lucia-malickova/manta-chair/MANTA_LIGHT/27_SEG_13L.stl

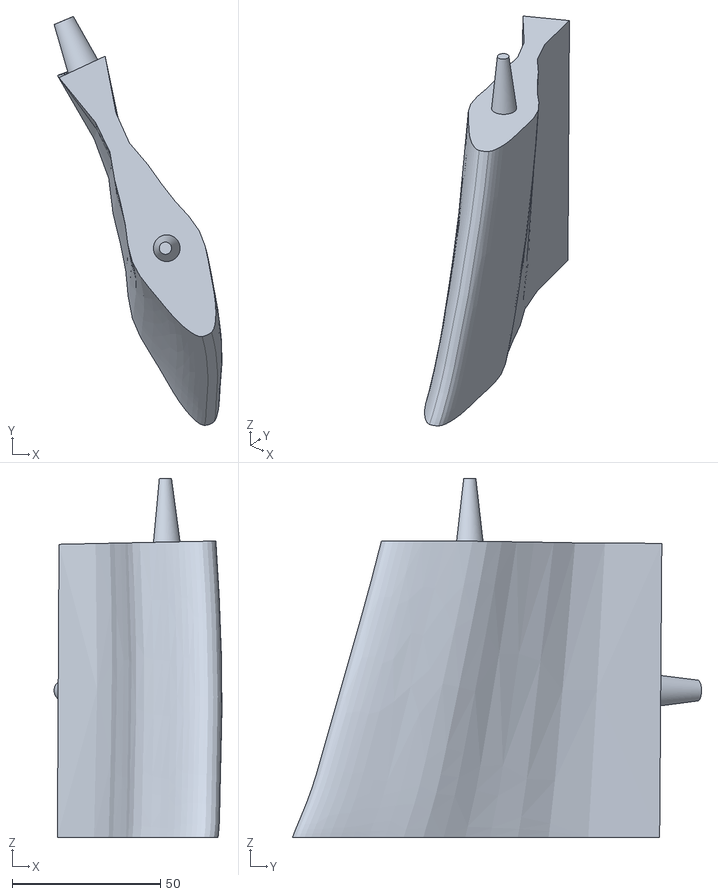
[picture p18: CAD file, 2026-09-29]
MANTA_LIGHT/27_SEG_13L.stl
56.6 x 138.1 x 121.2
