lucia-malickova/manta-chair/MANTA_RIBBON/41_SEG_22R.stl

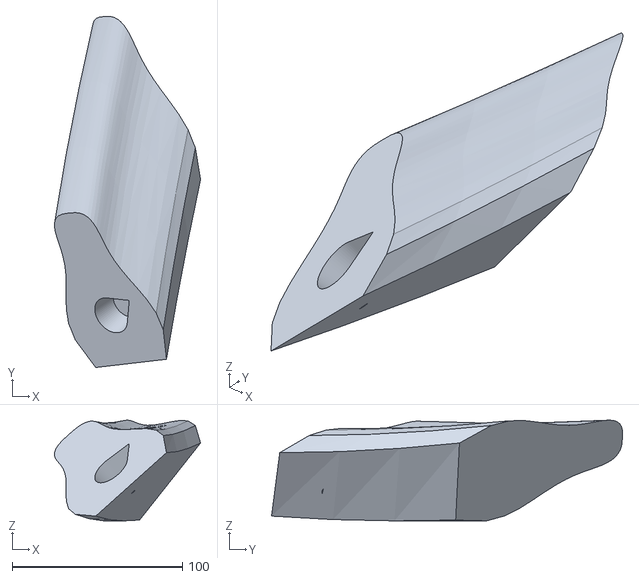
[picture p19: CAD file, 2026-09-29]
MANTA_RIBBON/41_SEG_22R.stl
85.9 x 206.4 x 59.2
