lucia-malickova/manta-chair/MANTA_LIGHT/04_SEG_01R.stl

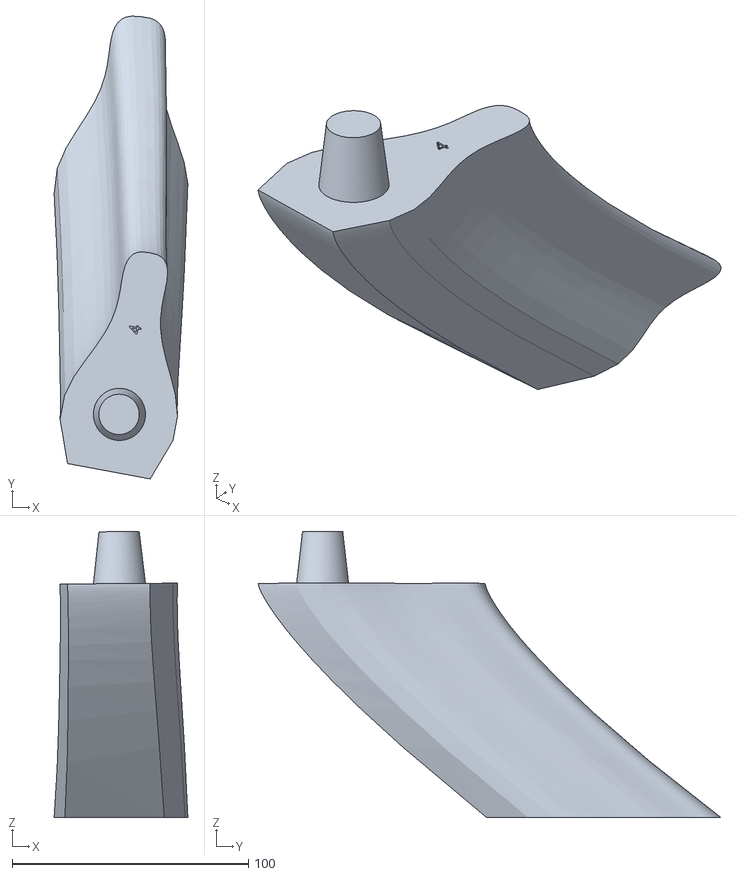
[picture p20: CAD file, 2026-09-29]
MANTA_LIGHT/04_SEG_01R.stl
56.7 x 196.1 x 121.2
