lucia-malickova/manta-chair/MANTA_RIBBON/26_SEG_12R.stl

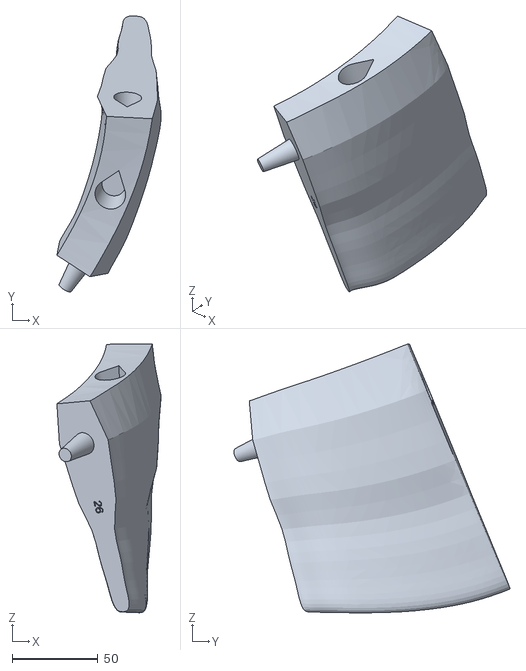
[picture p21: CAD file, 2026-09-29]
MANTA_RIBBON/26_SEG_12R.stl
60.6 x 160.6 x 156.3
