lucia-malickova/manta-chair/MANTA_LIGHT/03_SEG_01L.stl

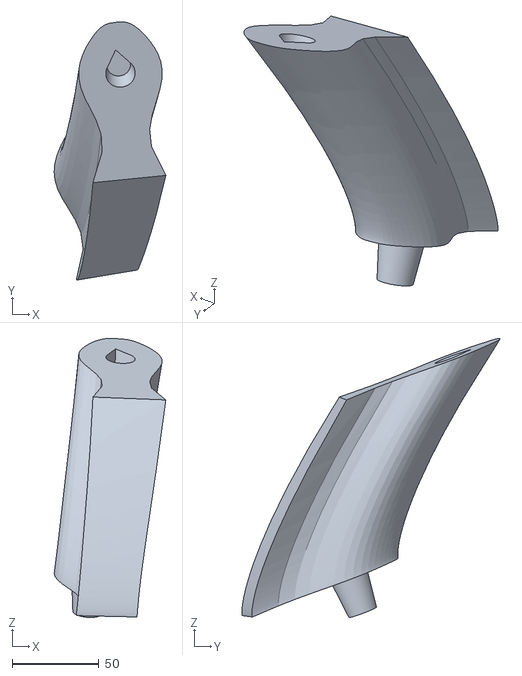
[picture p22: CAD file, 2026-09-29]
MANTA_LIGHT/03_SEG_01L.stl
64.5 x 149.1 x 161.1
