lucia-malickova/manta-chair/MANTA_RIBBON/29_SEG_14.stl

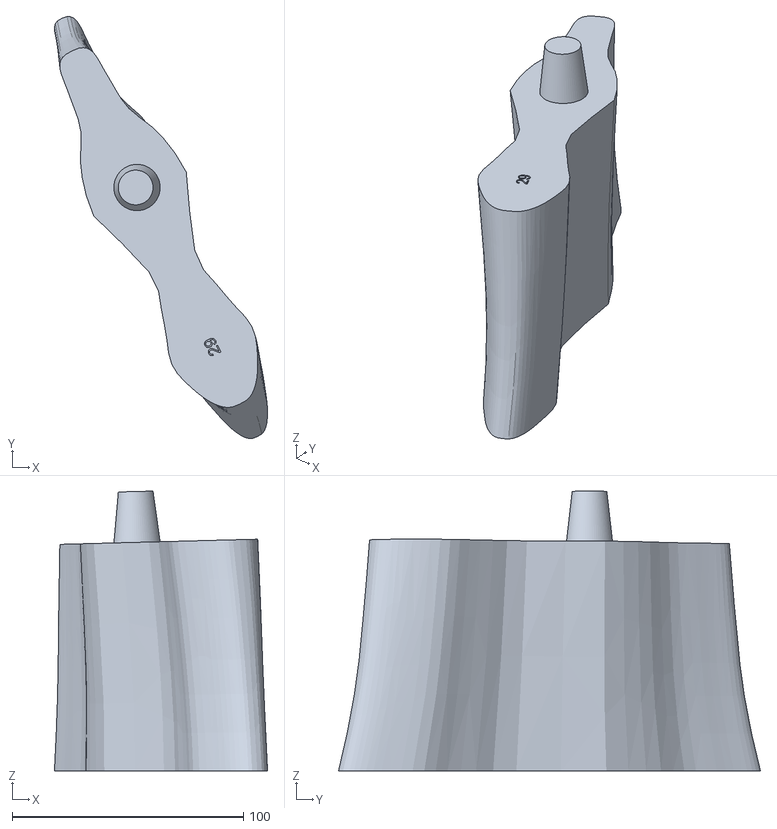
[picture p23: CAD file, 2026-09-29]
MANTA_RIBBON/29_SEG_14.stl
92.2 x 182.6 x 121.1
