lucia-malickova/manta-chair/MANTA_LIGHT/05_SEG_02L.stl

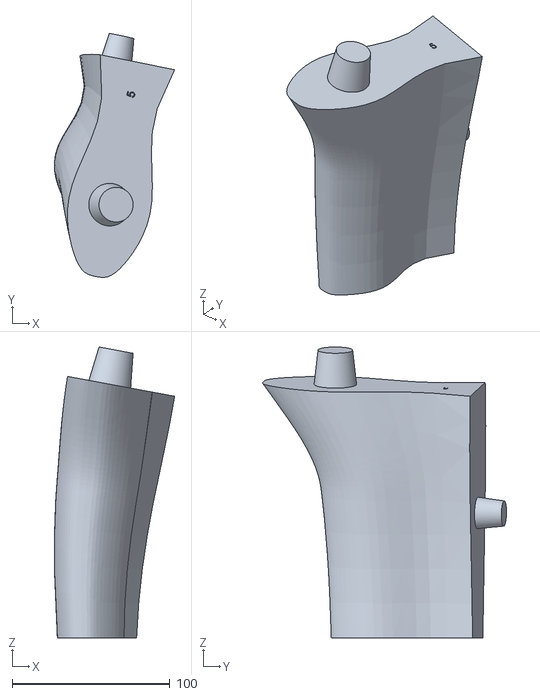
[picture p24: CAD file, 2026-09-29]
MANTA_LIGHT/05_SEG_02L.stl
76.4 x 154.9 x 184.7
