lucia-malickova/manta-chair/MANTA_RIBBON/07_SEG_03L.stl

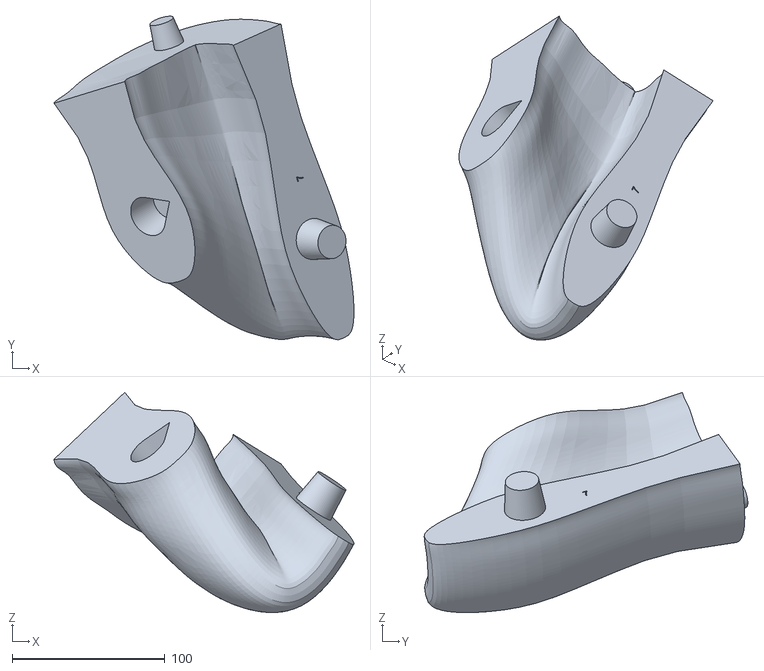
[picture p25: CAD file, 2026-09-29]
MANTA_RIBBON/07_SEG_03L.stl
196.5 x 212.0 x 144.2
