lucia-malickova/manta-chair/MANTA_LIGHT/17_SEG_08L.stl

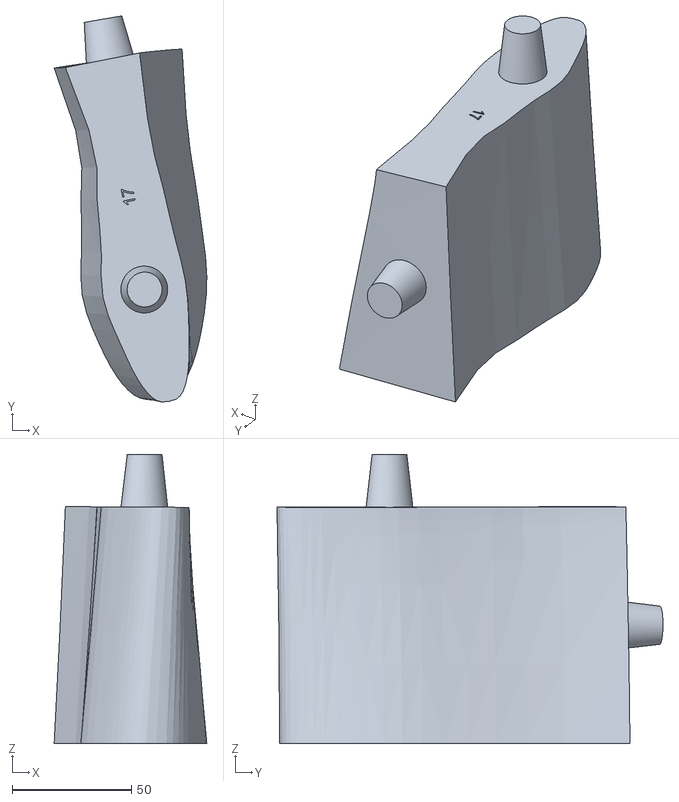
[picture p26: CAD file, 2026-09-29]
MANTA_LIGHT/17_SEG_08L.stl
63.9 x 161.6 x 121.0
