lucia-malickova/manta-chair/MANTA_RIBBON/09_SEG_04L.stl

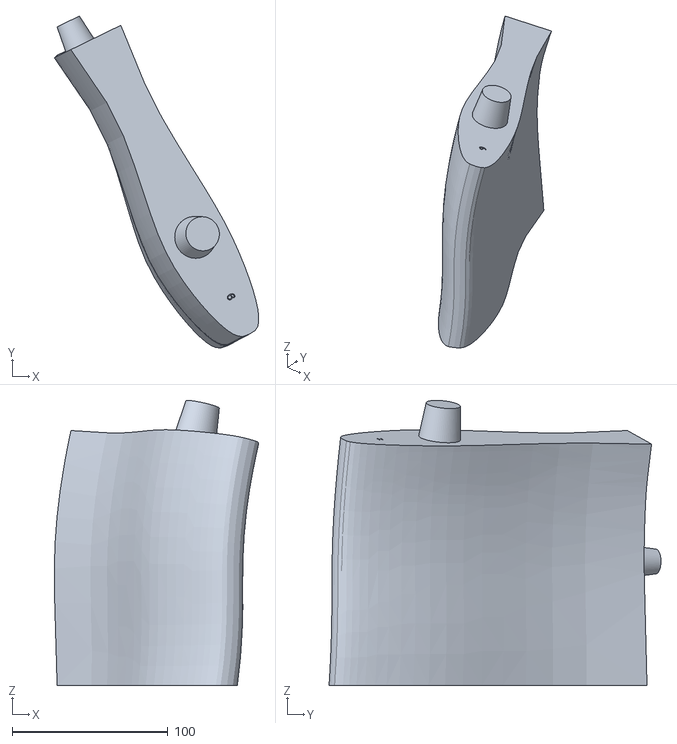
[picture p27: CAD file, 2026-09-29]
MANTA_RIBBON/09_SEG_04L.stl
131.2 x 213.1 x 183.1
