lucia-malickova/manta-chair/MANTA_LIGHT/40_SEG_22L.stl

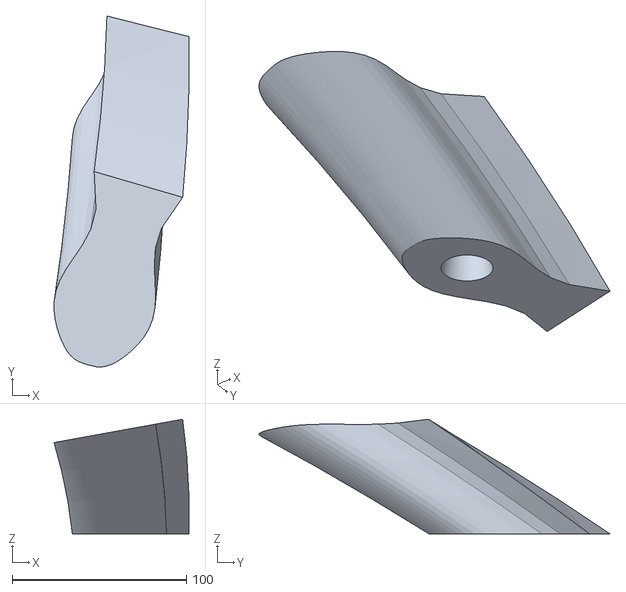
[picture p28: CAD file, 2026-09-29]
MANTA_LIGHT/40_SEG_22L.stl
77.3 x 201.2 x 65.7
