lucia-malickova/manta-chair/MANTA_RIBBON/19_SEG_09L.stl

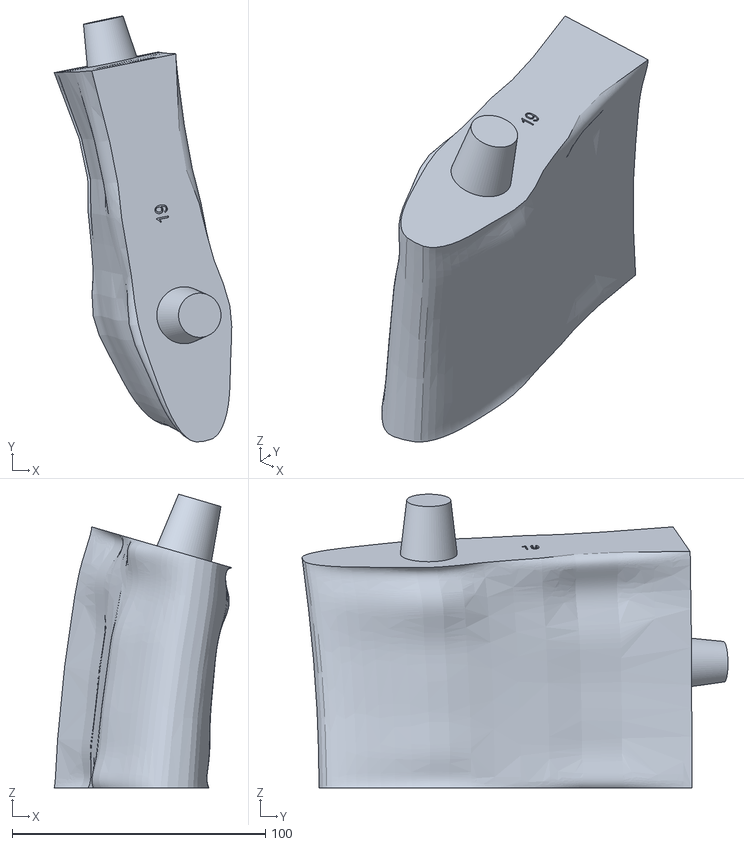
[picture p29: CAD file, 2026-09-29]
MANTA_RIBBON/19_SEG_09L.stl
70.2 x 168.3 x 116.0
