lucia-malickova/manta-chair/MANTA_LIGHT/02_SEG_00R.stl

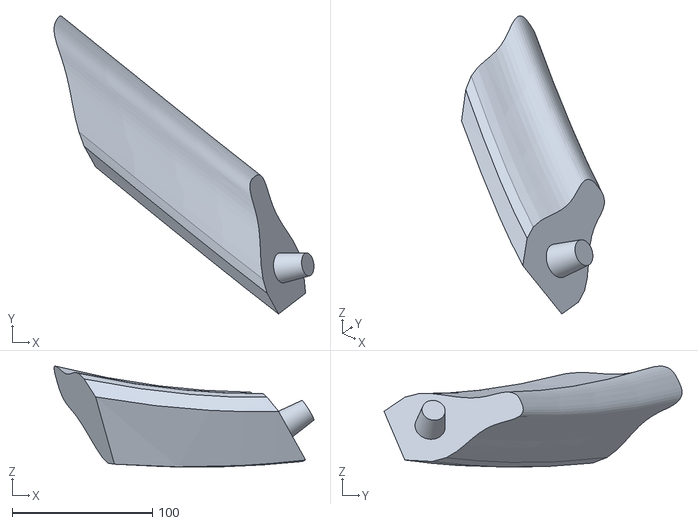
[picture p30: CAD file, 2026-09-29]
MANTA_LIGHT/02_SEG_00R.stl
185.1 x 212.2 x 71.7
