lucia-malickova/manta-chair/MANTA_RIBBON/04_SEG_01R.stl

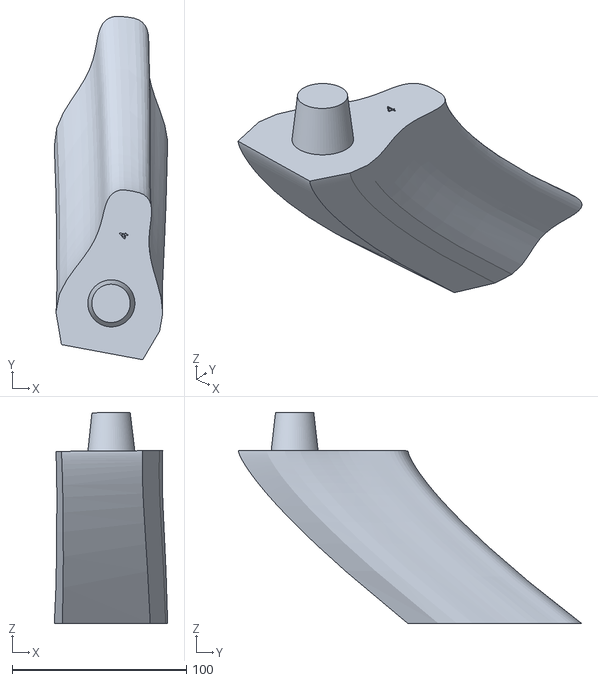
[picture p31: CAD file, 2026-09-29]
MANTA_RIBBON/04_SEG_01R.stl
65.1 x 197.3 x 121.2
