lucia-malickova/manta-chair/MANTA_LIGHT/06_SEG_02R.stl

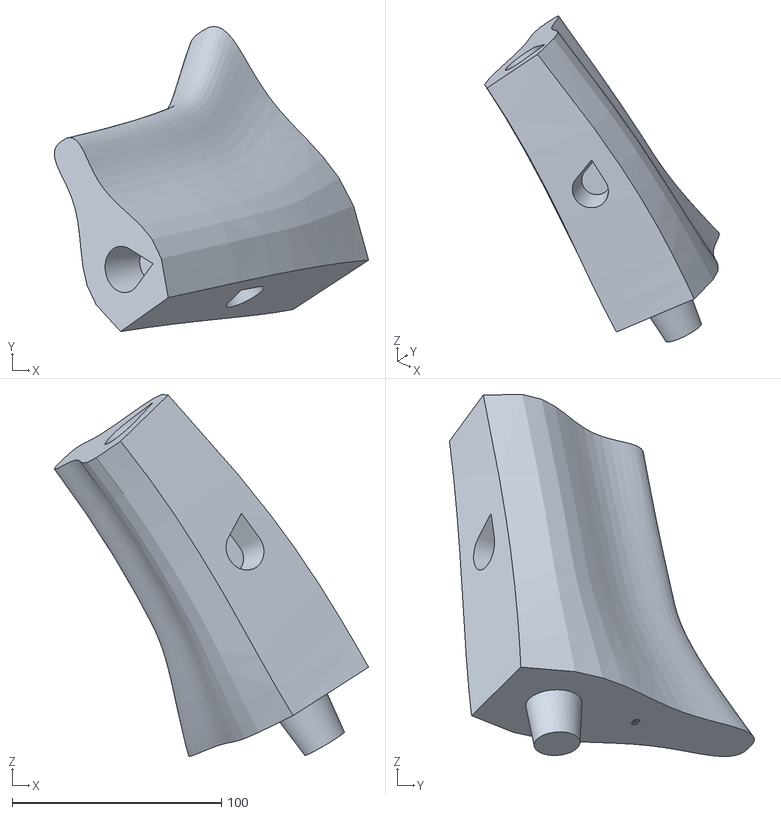
[picture p32: CAD file, 2026-09-29]
MANTA_LIGHT/06_SEG_02R.stl
150.3 x 145.9 x 173.1
