lucia-malickova/manta-chair/MANTA_RIBBON/20_SEG_09R.stl

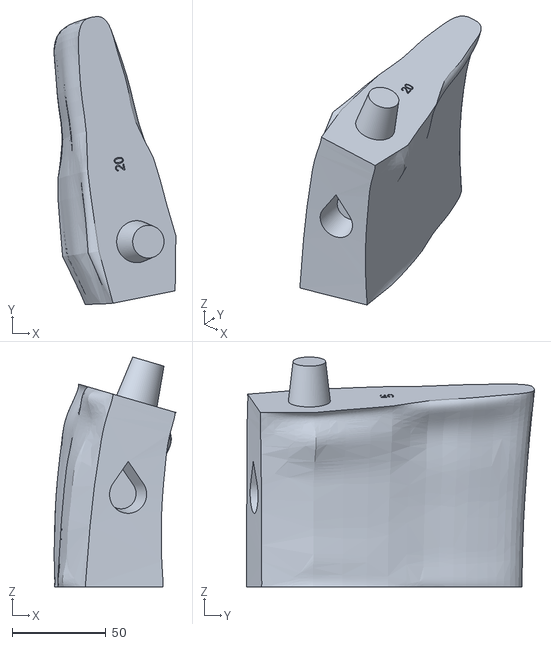
[picture p33: CAD file, 2026-09-29]
MANTA_RIBBON/20_SEG_09R.stl
65.1 x 154.0 x 122.9
