lucia-malickova/manta-chair/MANTA_LIGHT/10_SEG_04R.stl

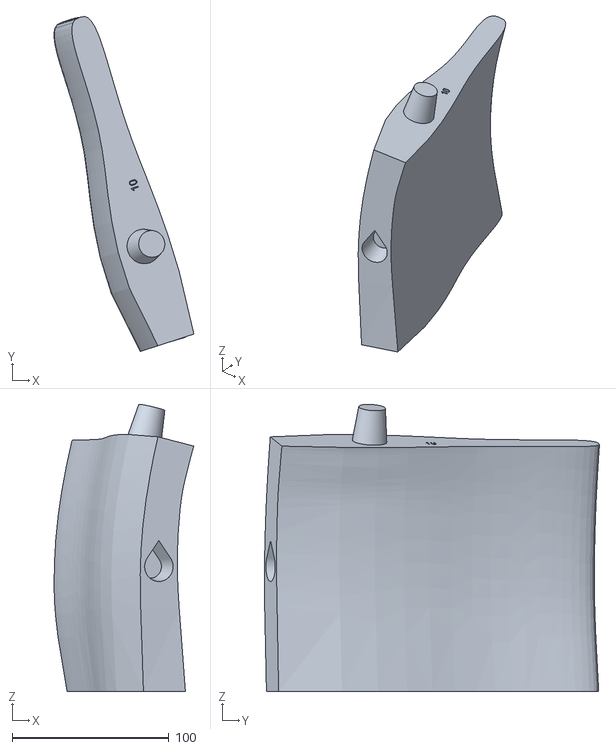
[picture p34: CAD file, 2026-09-29]
MANTA_LIGHT/10_SEG_04R.stl
89.1 x 213.4 x 183.0
