lucia-malickova/manta-chair/MANTA_RIBBON/32_SEG_17.stl

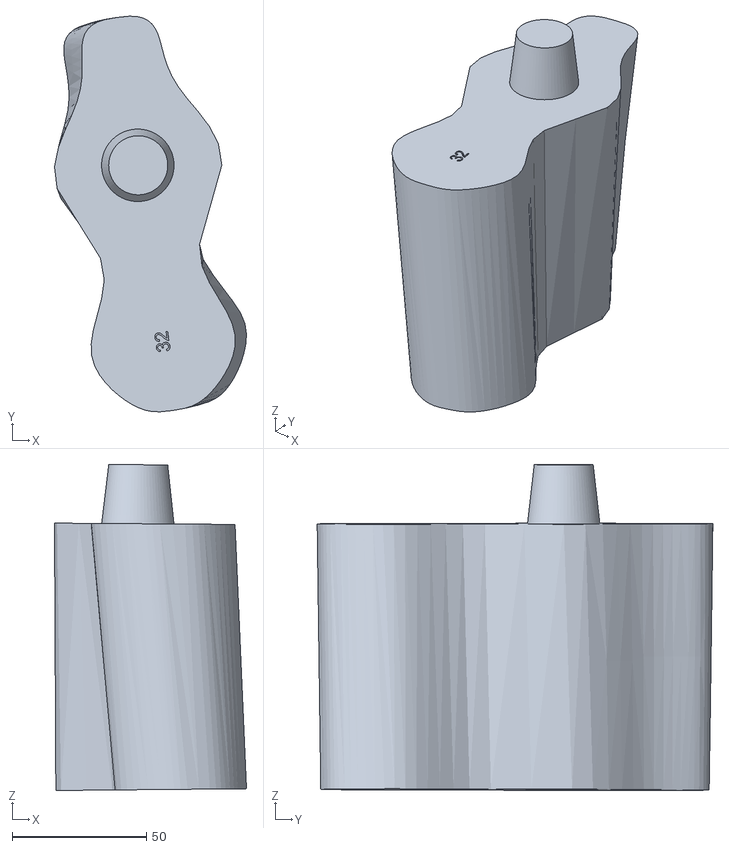
[picture p35: CAD file, 2026-09-29]
MANTA_RIBBON/32_SEG_17.stl
71.6 x 147.5 x 121.5
