lucia-malickova/manta-chair/MANTA_LIGHT/28_SEG_13R.stl

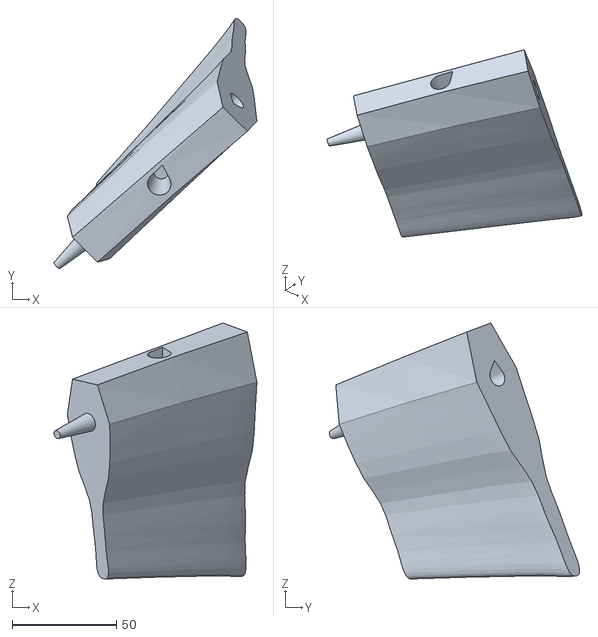
[picture p36: CAD file, 2026-09-29]
MANTA_LIGHT/28_SEG_13R.stl
97.5 x 120.3 x 123.0
