lucia-malickova/manta-chair/MANTA_RIBBON/35_SEG_19R.stl

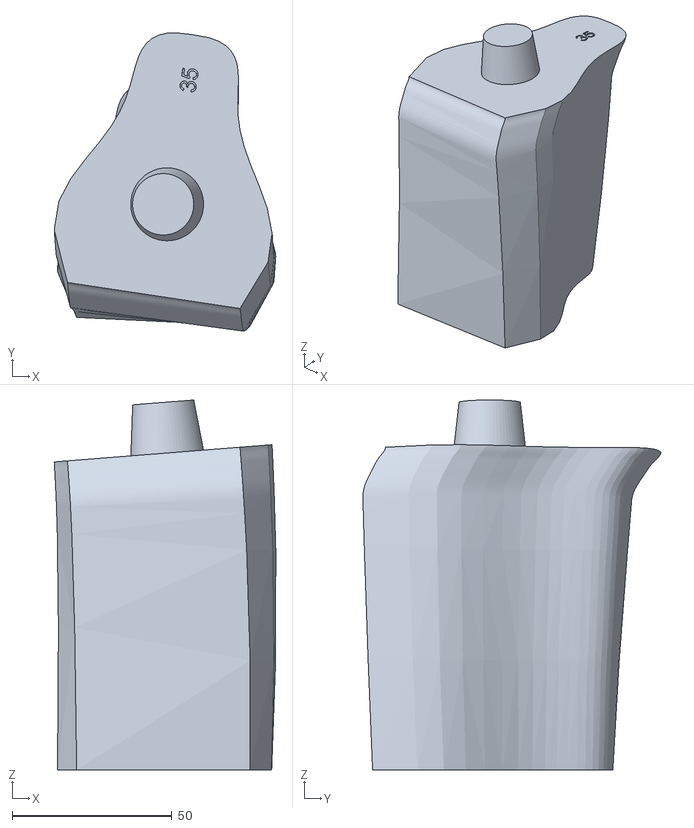
[picture p37: CAD file, 2026-09-29]
MANTA_RIBBON/35_SEG_19R.stl
69.5 x 93.5 x 116.0
