lucia-malickova/manta-chair/MANTA_LIGHT/33_SEG_18.stl

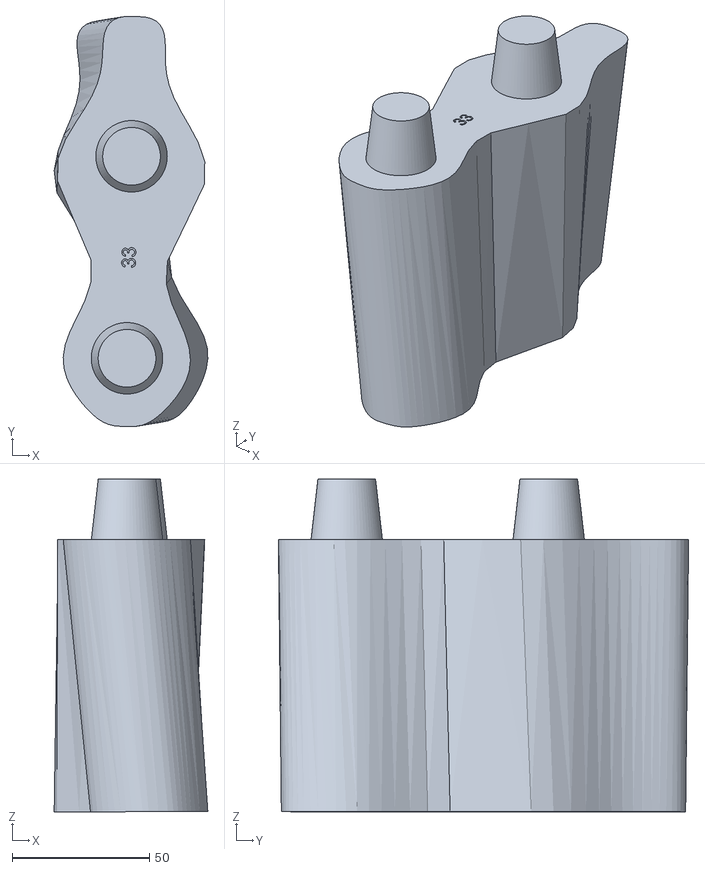
[picture p38: CAD file, 2026-09-29]
MANTA_LIGHT/33_SEG_18.stl
56.0 x 149.4 x 121.2
