lucia-malickova/manta-chair/MANTA_RIBBON/06_SEG_02R.stl

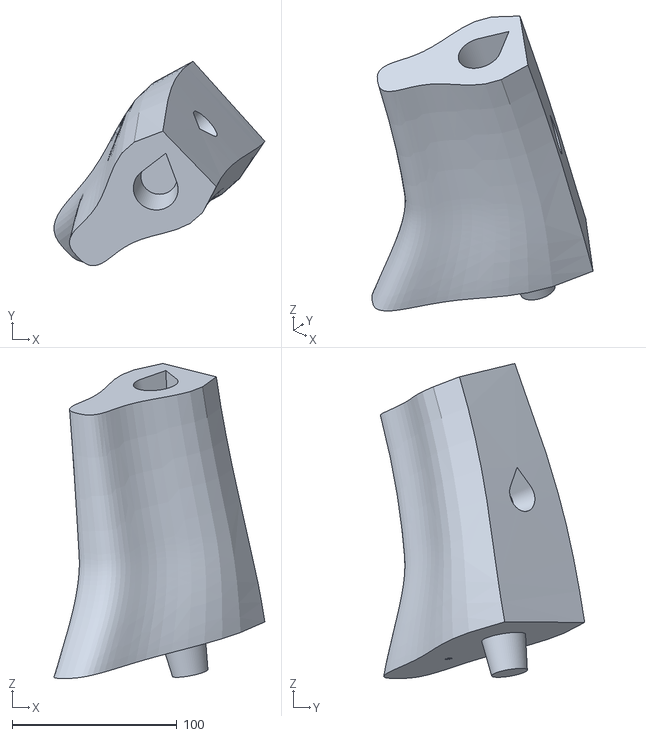
[picture p39: CAD file, 2026-09-29]
MANTA_RIBBON/06_SEG_02R.stl
128.1 x 124.2 x 191.4
