lucia-malickova/manta-chair/MANTA_LIGHT/34_SEG_19L.stl

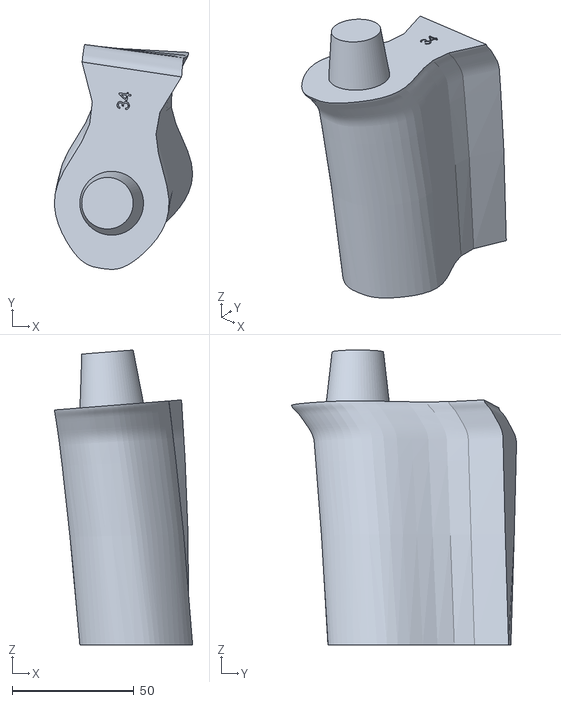
[picture p40: CAD file, 2026-09-29]
MANTA_LIGHT/34_SEG_19L.stl
56.8 x 92.4 x 121.2
