lucia-malickova/manta-chair/MANTA_RIBBON/33_SEG_18.stl

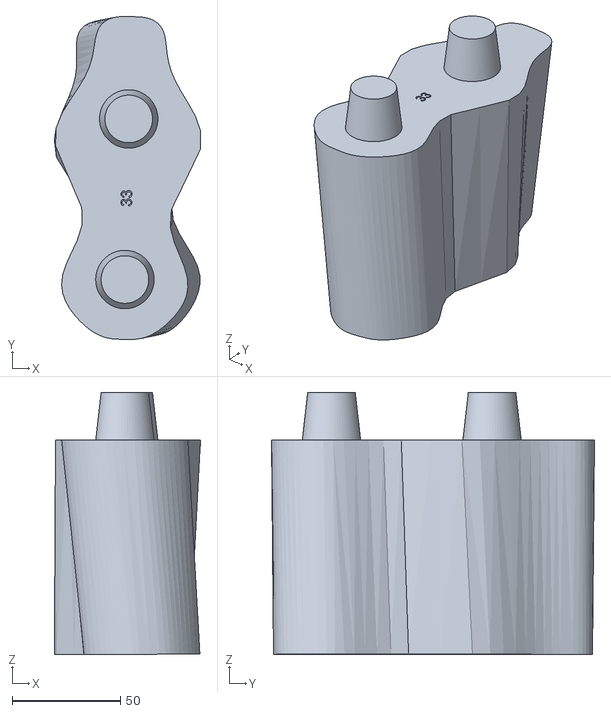
[picture p41: CAD file, 2026-09-29]
MANTA_RIBBON/33_SEG_18.stl
67.7 x 149.4 x 121.3
