lucia-malickova/manta-chair/MANTA_LIGHT/22_SEG_10R.stl

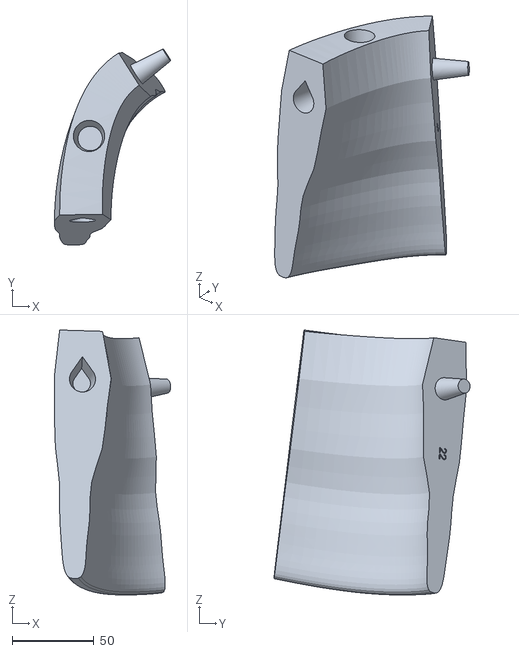
[picture p42: CAD file, 2026-09-29]
MANTA_LIGHT/22_SEG_10R.stl
71.0 x 119.6 x 161.6
