lucia-malickova/manta-chair/MANTA_RIBBON/37_SEG_20R.stl

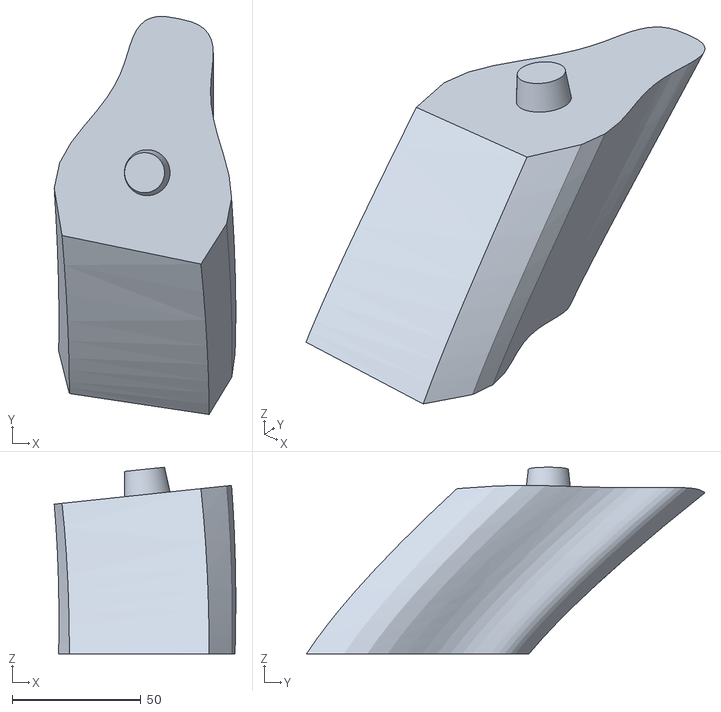
[picture p43: CAD file, 2026-09-29]
MANTA_RIBBON/37_SEG_20R.stl
70.5 x 154.5 x 72.4
