lucia-malickova/manta-chair/MANTA_LIGHT/37_SEG_20R.stl

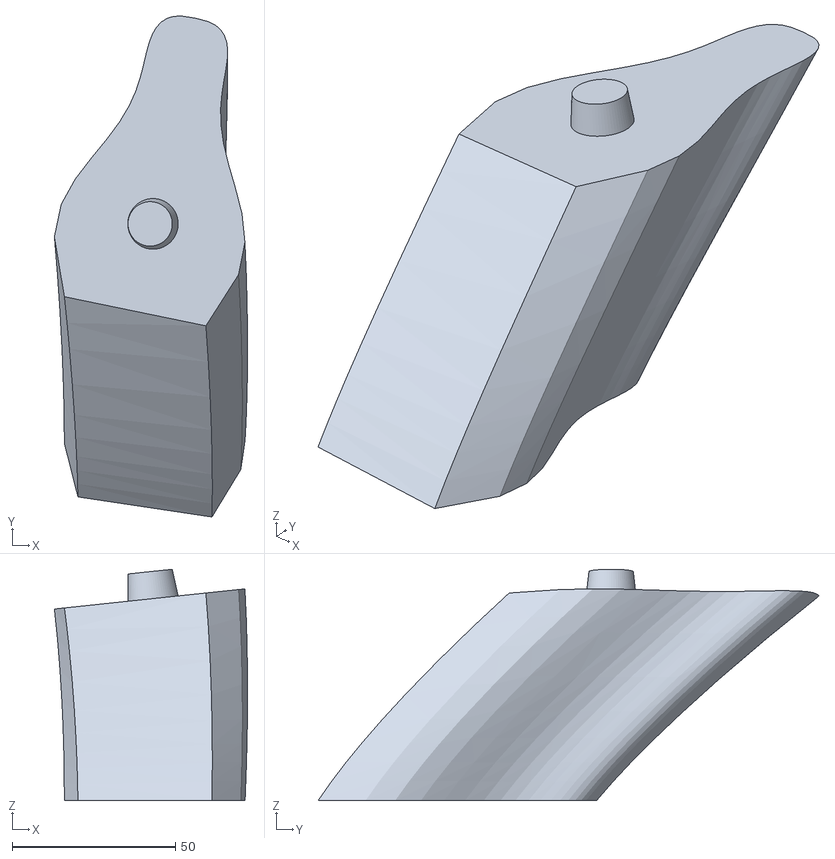
[picture p44: CAD file, 2026-09-29]
MANTA_LIGHT/37_SEG_20R.stl
59.1 x 153.3 x 70.8
