lucia-malickova/manta-chair/MANTA_RIBBON/11_SEG_05L.stl

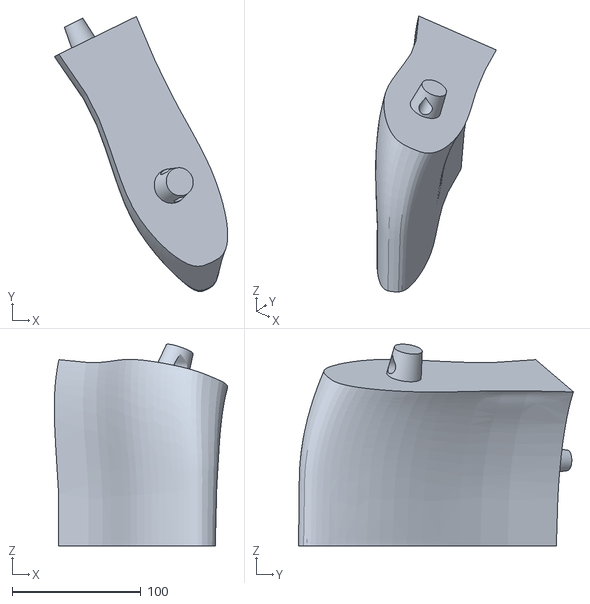
[picture p45: CAD file, 2026-09-29]
MANTA_RIBBON/11_SEG_05L.stl
134.5 x 213.2 x 156.4
