lucia-malickova/manta-chair/MANTA_LIGHT/08_SEG_03R.stl

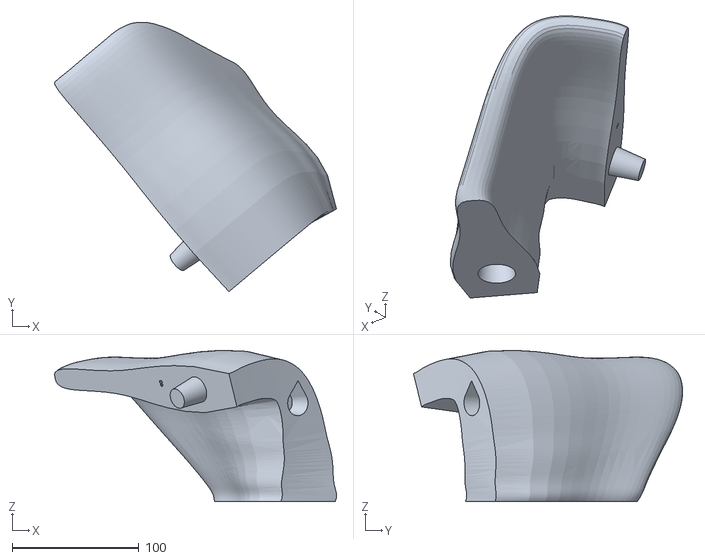
[picture p46: CAD file, 2026-09-29]
MANTA_LIGHT/08_SEG_03R.stl
222.8 x 212.7 x 119.6
