lucia-malickova/manta-chair/MANTA_RIBBON/30_SEG_15.stl

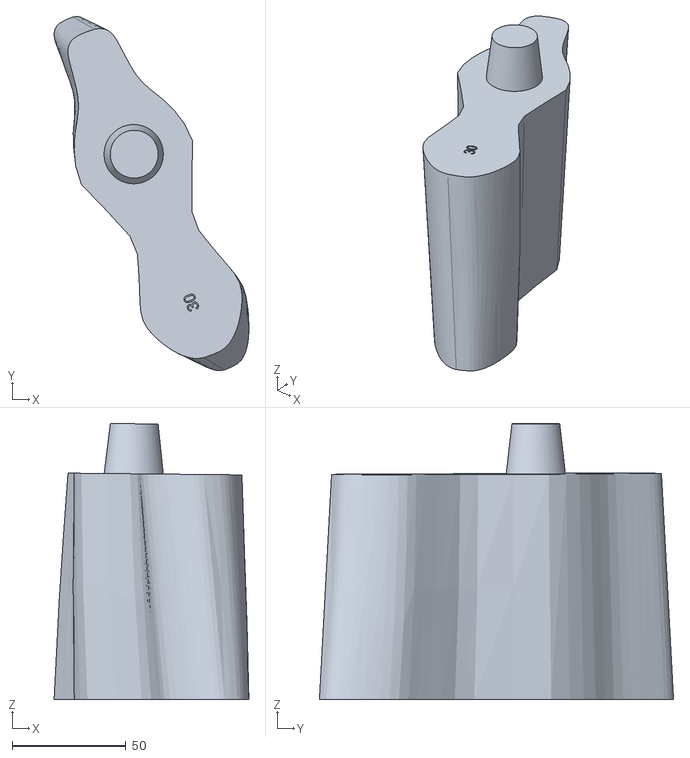
[picture p47: CAD file, 2026-09-29]
MANTA_RIBBON/30_SEG_15.stl
85.7 x 155.7 x 121.3
