lucia-malickova/manta-chair/MANTA_LIGHT/11_SEG_05L.stl

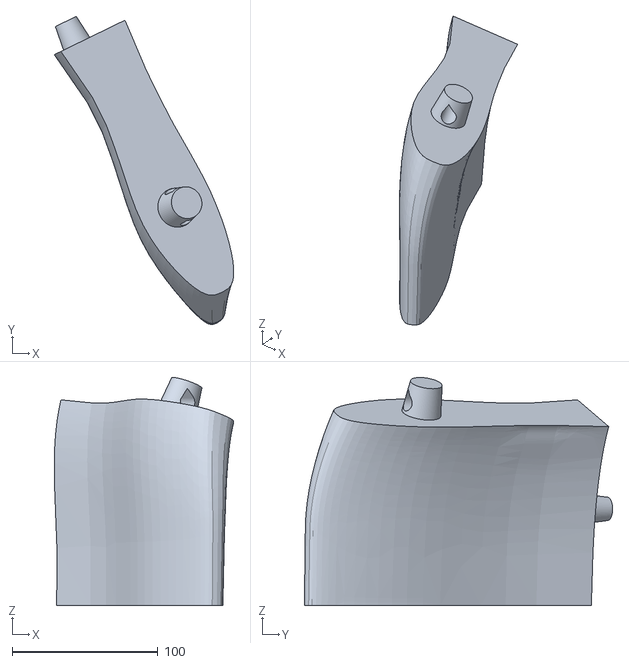
[picture p48: CAD file, 2026-09-29]
MANTA_LIGHT/11_SEG_05L.stl
123.1 x 211.4 x 156.4
