lucia-malickova/manta-chair/MANTA_RIBBON/27_SEG_13L.stl

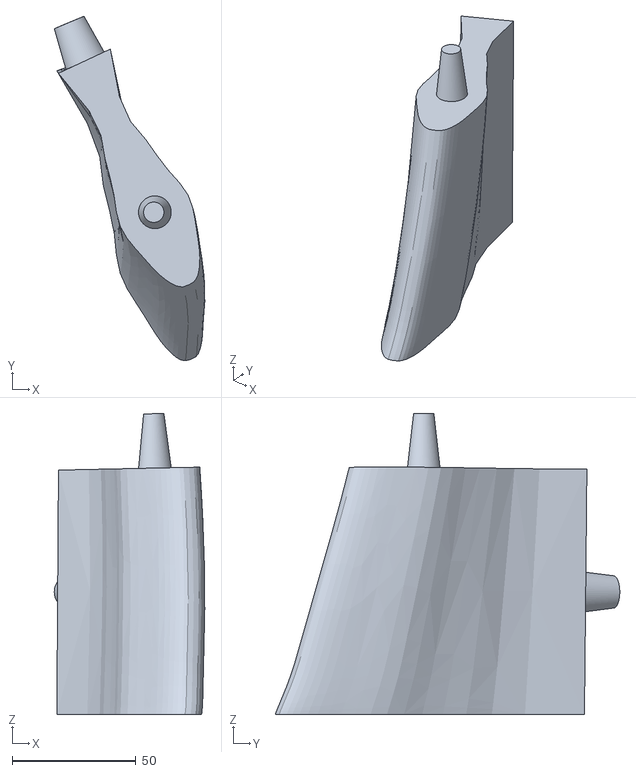
[picture p49: CAD file, 2026-09-29]
MANTA_RIBBON/27_SEG_13L.stl
60.9 x 139.5 x 121.8
