lucia-malickova/manta-chair/MANTA_LIGHT/21_SEG_10L.stl

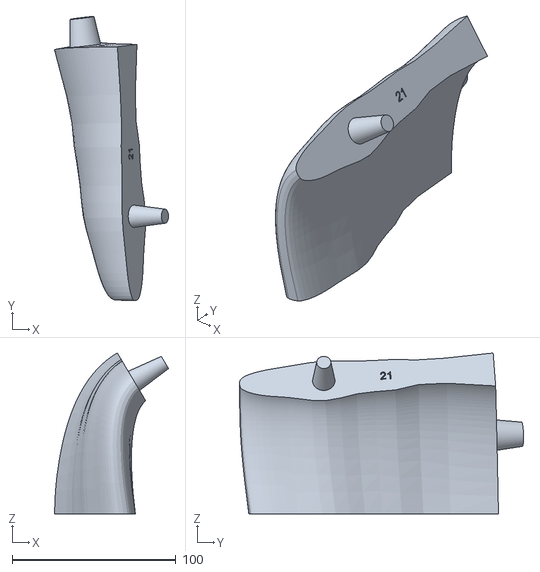
[picture p50: CAD file, 2026-09-29]
MANTA_LIGHT/21_SEG_10L.stl
69.6 x 173.3 x 98.2
