lucia-malickova/manta-chair/MANTA_RIBBON/22_SEG_10R.stl

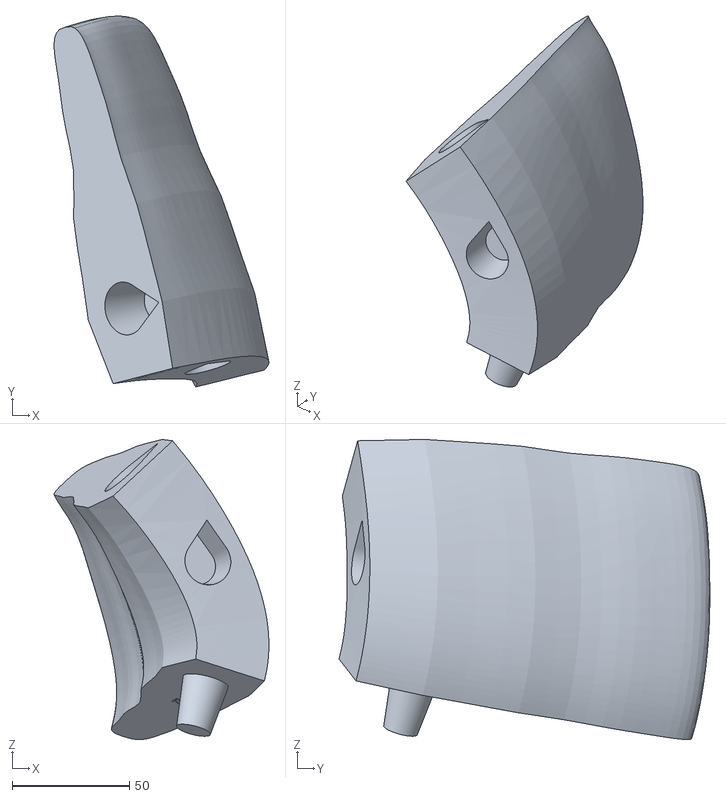
[picture p51: CAD file, 2026-09-29]
MANTA_RIBBON/22_SEG_10R.stl
91.6 x 158.2 x 127.9
