lucia-malickova/manta-chair/MANTA_LIGHT/24_SEG_11R.stl

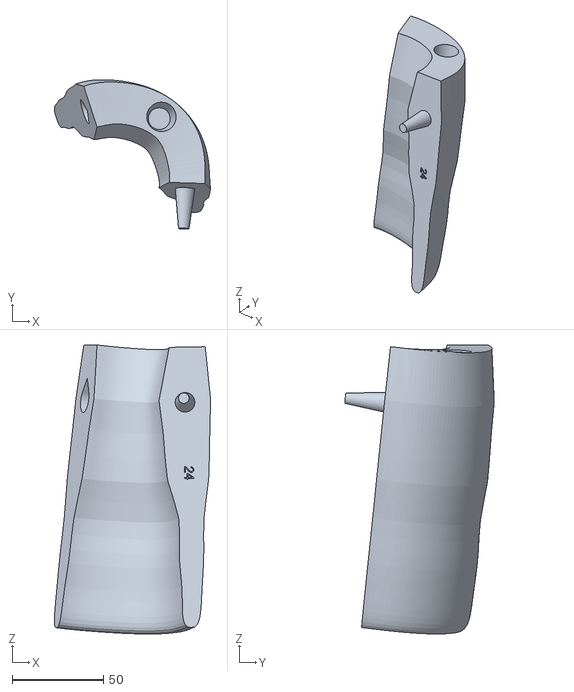
[picture p52: CAD file, 2026-09-29]
MANTA_LIGHT/24_SEG_11R.stl
85.4 x 81.7 x 158.0
