lucia-malickova/manta-chair/MANTA_RIBBON/14_SEG_06R.stl

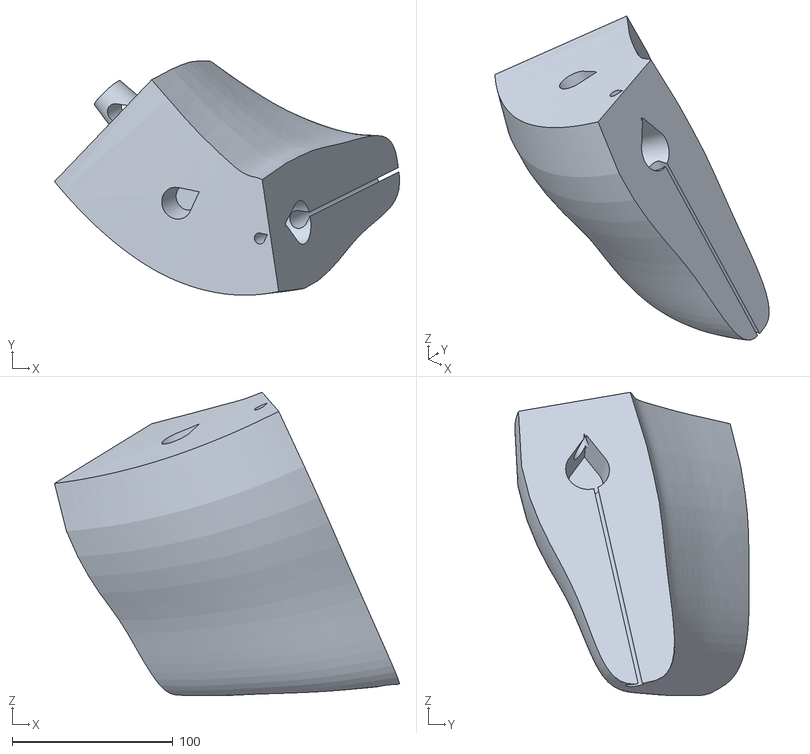
[picture p53: CAD file, 2026-09-29]
MANTA_RIBBON/14_SEG_06R.stl
214.6 x 145.8 x 188.7
