lucia-malickova/manta-chair/MANTA_LIGHT/15_SEG_07L.stl

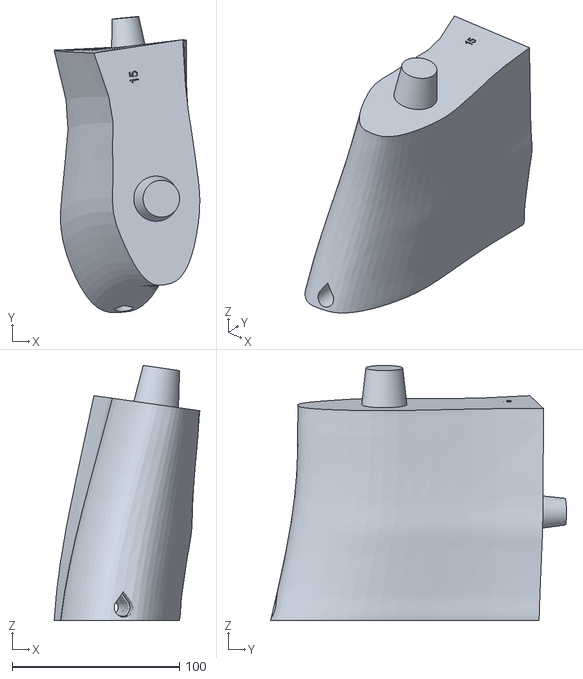
[picture p54: CAD file, 2026-09-29]
MANTA_LIGHT/15_SEG_07L.stl
87.1 x 176.8 x 152.4
