lucia-malickova/manta-chair/MANTA_RIBBON/38_SEG_21L.stl

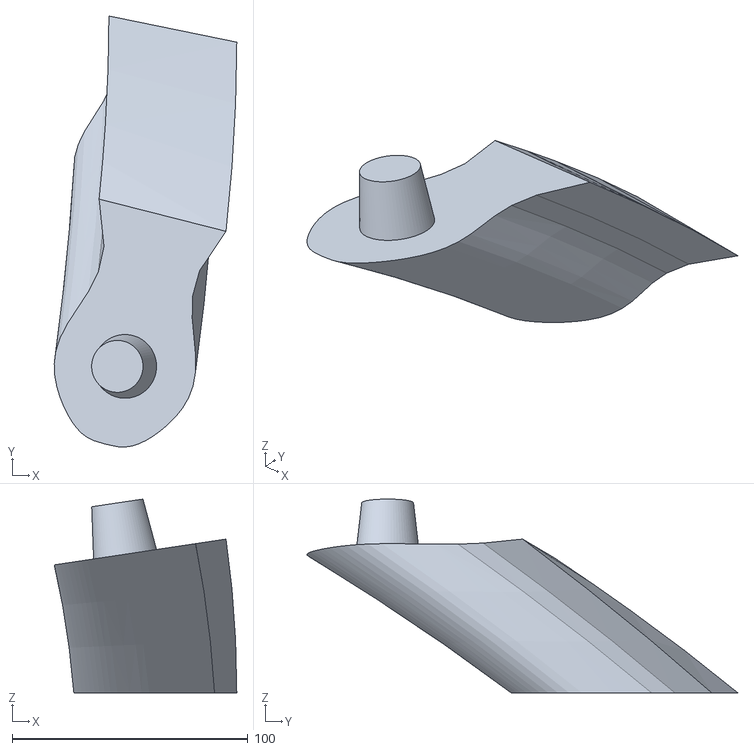
[picture p55: CAD file, 2026-09-29]
MANTA_RIBBON/38_SEG_21L.stl
77.4 x 182.7 x 82.2
