lucia-malickova/manta-chair/MANTA_LIGHT/41_SEG_22R.stl

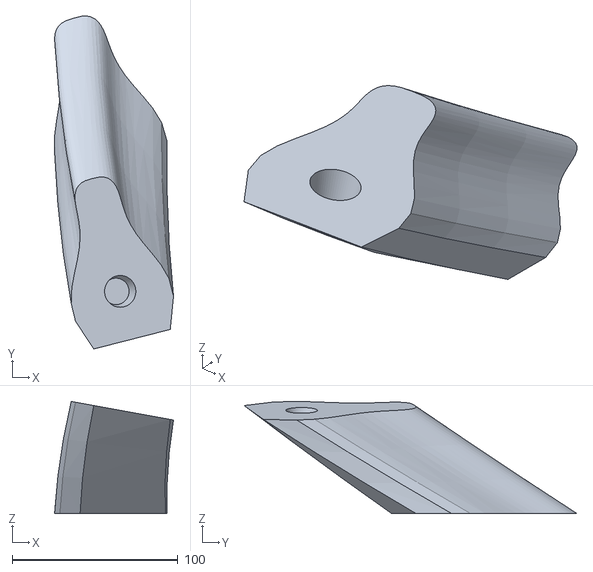
[picture p56: CAD file, 2026-09-29]
MANTA_LIGHT/41_SEG_22R.stl
71.9 x 201.1 x 67.7
