lucia-malickova/manta-chair/MANTA_RIBBON/36_SEG_20L.stl

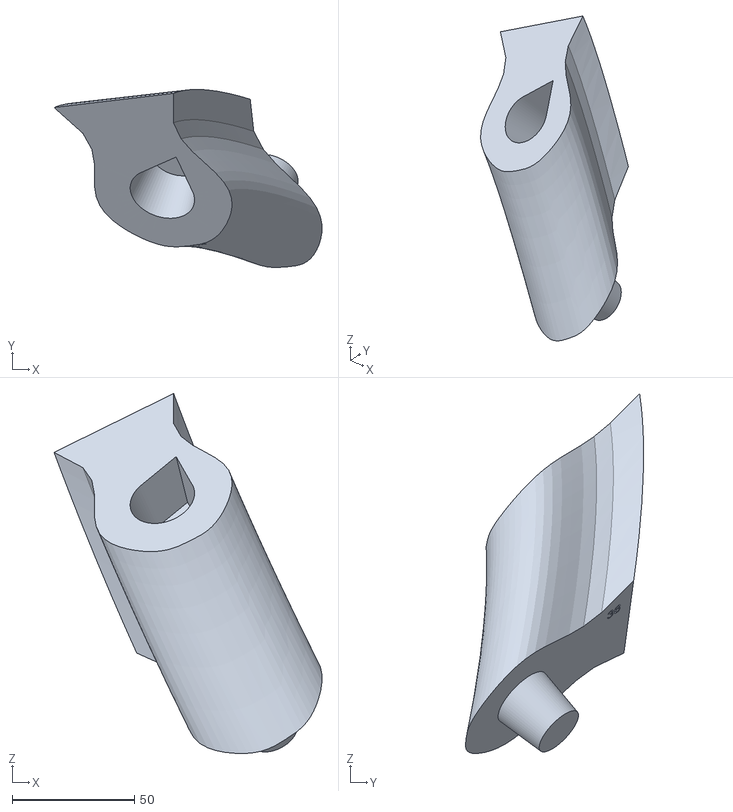
[picture p57: CAD file, 2026-09-29]
MANTA_RIBBON/36_SEG_20L.stl
109.6 x 72.9 x 147.3
