lucia-malickova/manta-chair/MANTA_LIGHT/19_SEG_09L.stl

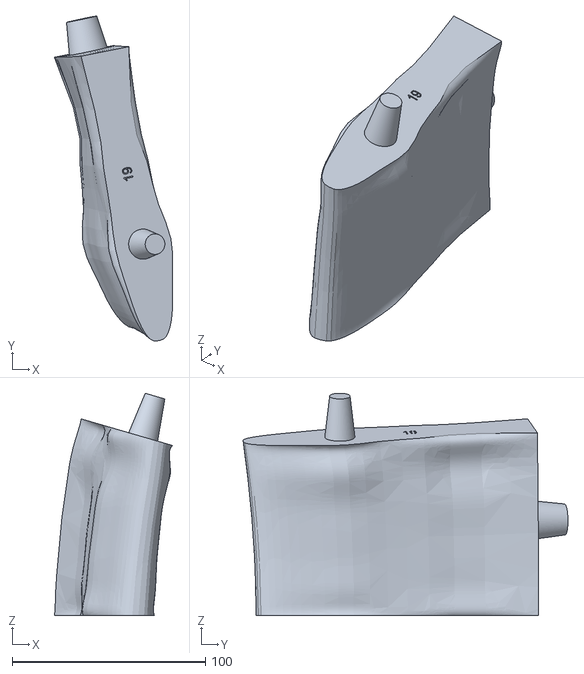
[picture p58: CAD file, 2026-09-29]
MANTA_LIGHT/19_SEG_09L.stl
61.2 x 168.1 x 115.1
