lucia-malickova/manta-chair/MANTA_RIBBON/16_SEG_07R.stl

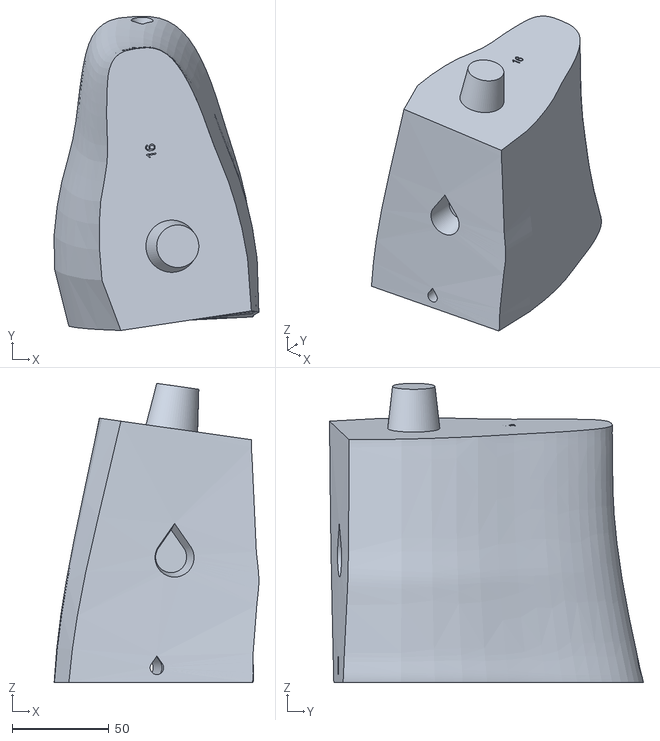
[picture p59: CAD file, 2026-09-29]
MANTA_RIBBON/16_SEG_07R.stl
106.0 x 162.5 x 155.0
