lucia-malickova/manta-chair/MANTA_LIGHT/20_SEG_09R.stl

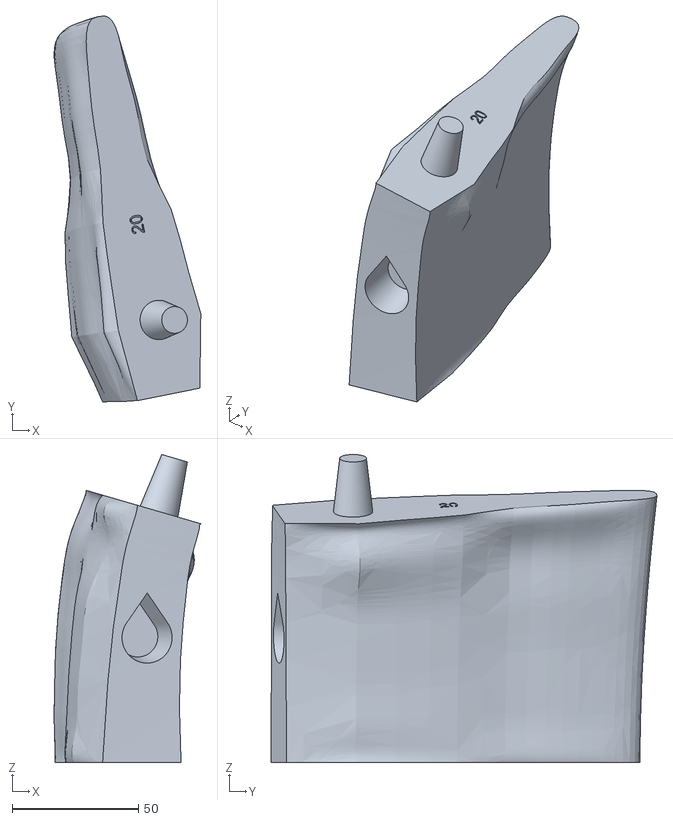
[picture p60: CAD file, 2026-09-29]
MANTA_LIGHT/20_SEG_09R.stl
58.1 x 152.8 x 122.0
