lucia-malickova/manta-chair/MANTA_RIBBON/10_SEG_04R.stl

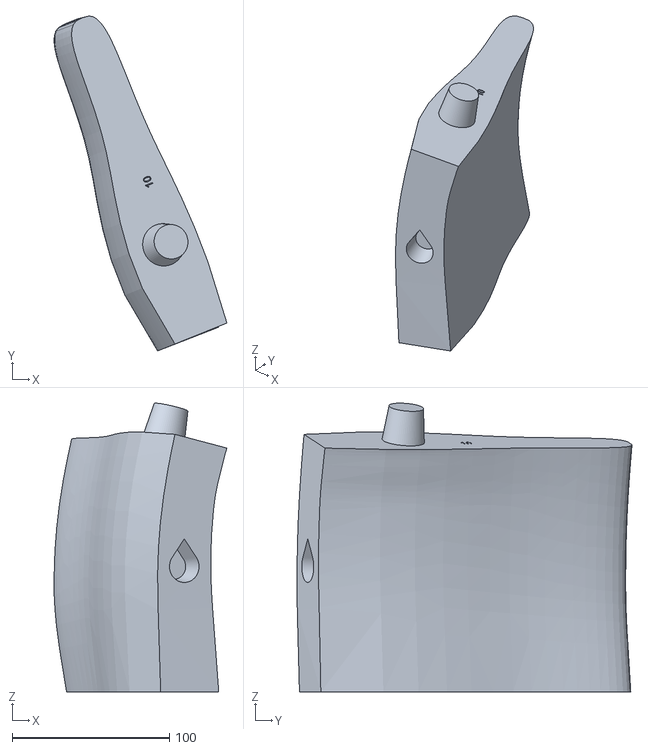
[picture p61: CAD file, 2026-09-29]
MANTA_RIBBON/10_SEG_04R.stl
109.9 x 213.0 x 183.6
