lucia-malickova/manta-chair/MANTA_LIGHT/26_SEG_12R.stl

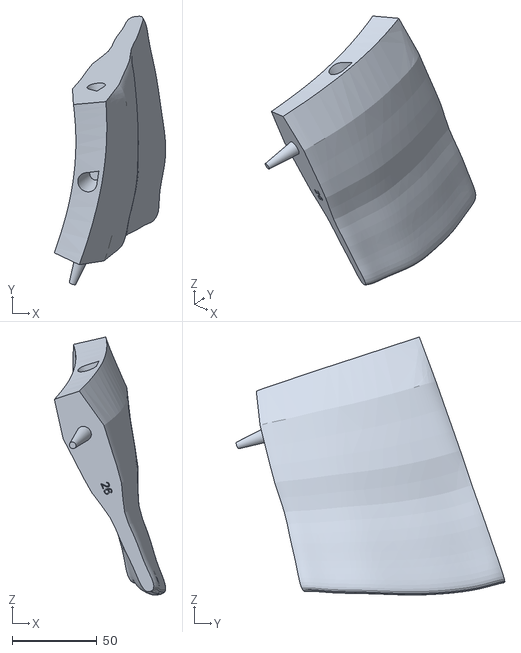
[picture p62: CAD file, 2026-09-29]
MANTA_LIGHT/26_SEG_12R.stl
65.7 x 158.6 x 152.3
