lucia-malickova/manta-chair/MANTA_RIBBON/42_PIN.stl

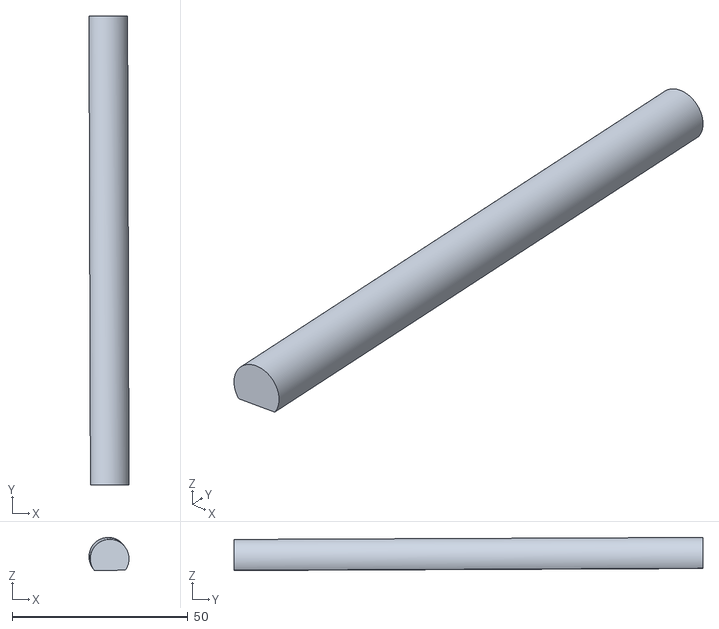
[picture p63: CAD file, 2026-09-29]
MANTA_RIBBON/42_PIN.stl
11.4 x 133.5 x 9.43
