lucia-malickova/manta-chair/MANTA_LIGHT/23_SEG_11L.stl

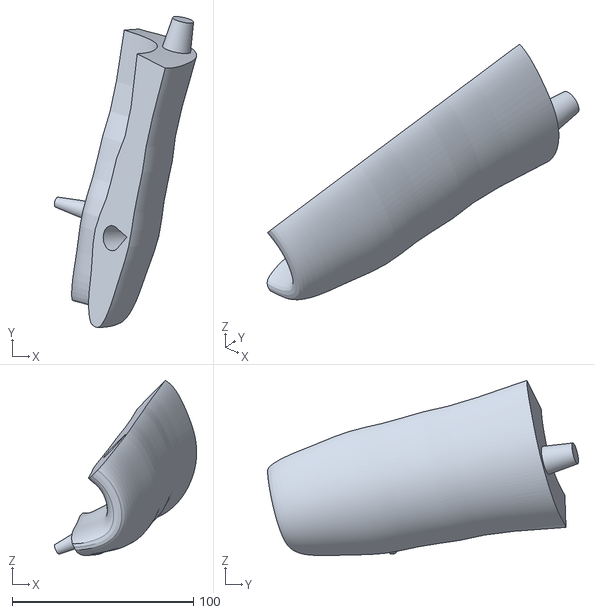
[picture p64: CAD file, 2026-09-29]
MANTA_LIGHT/23_SEG_11L.stl
78.4 x 171.4 x 96.6
