lucia-malickova/manta-chair/MANTA_RIBBON/21_SEG_10L.stl

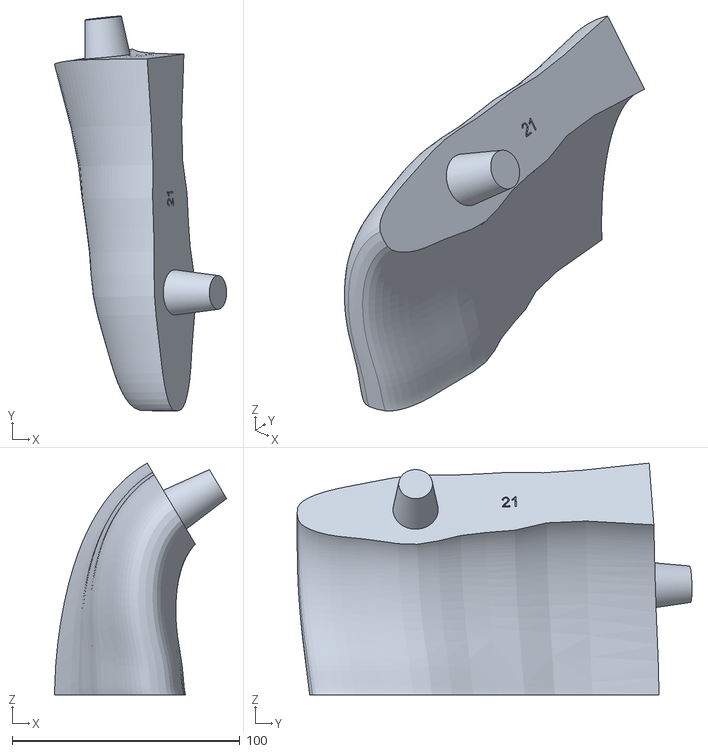
[picture p65: CAD file, 2026-09-29]
MANTA_RIBBON/21_SEG_10L.stl
75.6 x 173.3 x 101.7
