lucia-malickova/manta-chair/MANTA_LIGHT/16_SEG_07R.stl

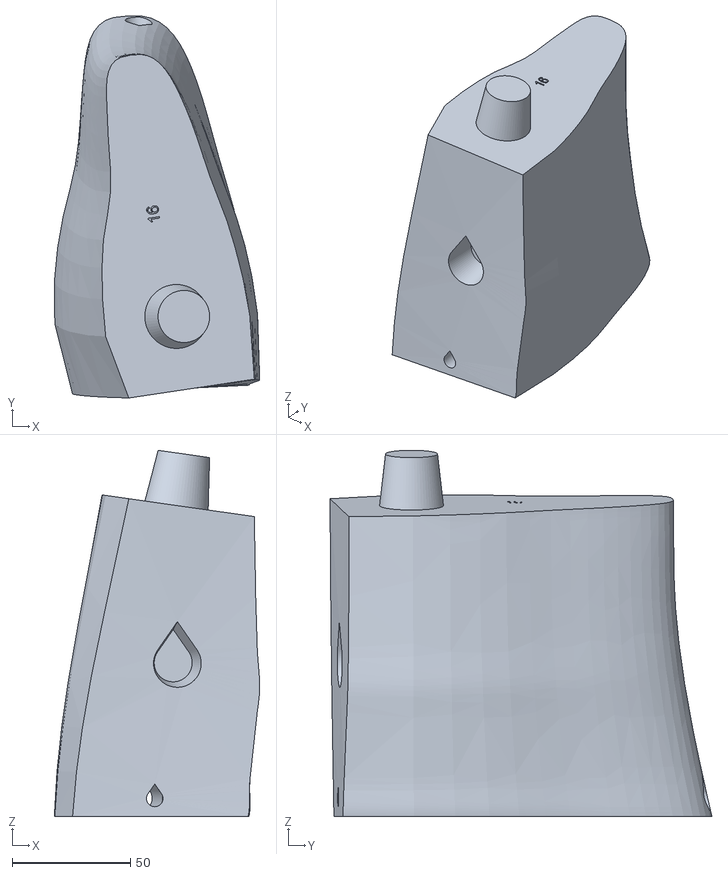
[picture p66: CAD file, 2026-09-29]
MANTA_LIGHT/16_SEG_07R.stl
86.8 x 161.4 x 154.8
