lucia-malickova/manta-chair/MANTA_RIBBON/17_SEG_08L.stl

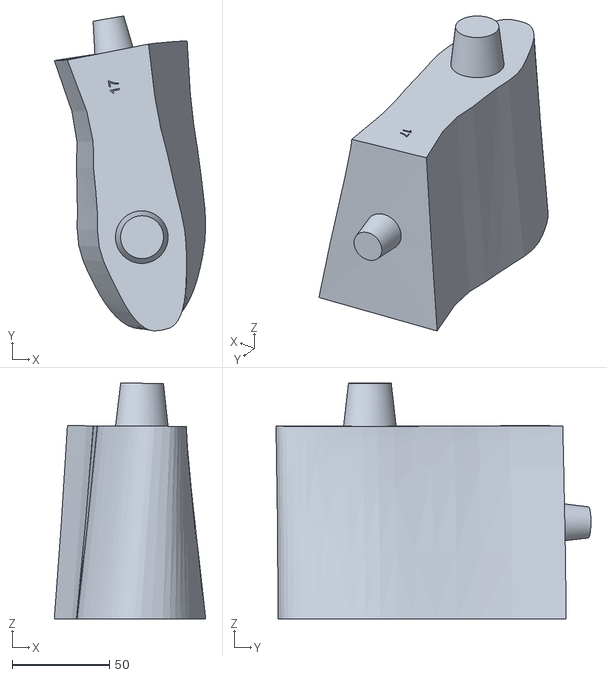
[picture p67: CAD file, 2026-09-29]
MANTA_RIBBON/17_SEG_08L.stl
77.8 x 161.7 x 121.1
