lucia-malickova/manta-chair/MANTA_LIGHT/01_SEG_00L.stl

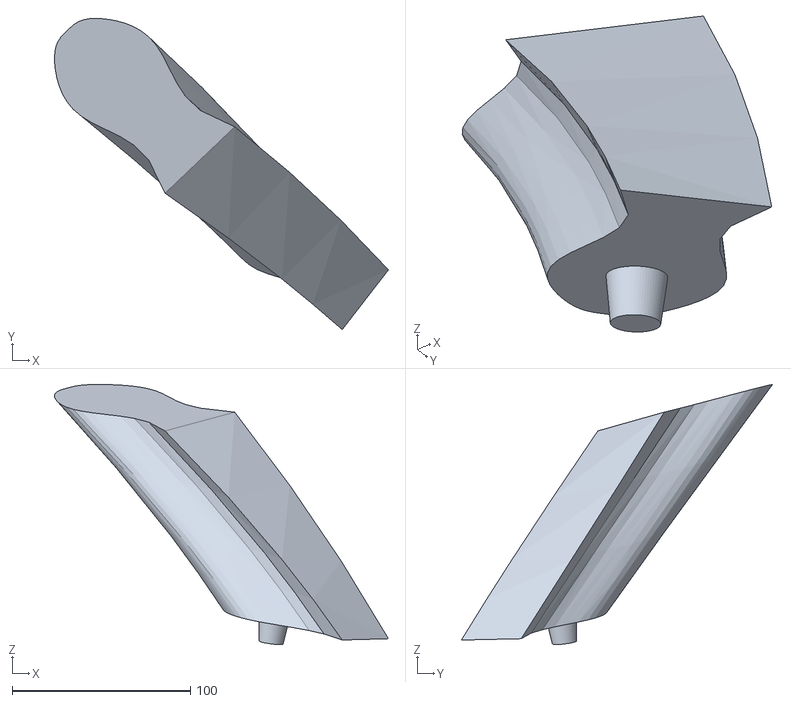
[picture p68: CAD file, 2026-09-29]
MANTA_LIGHT/01_SEG_00L.stl
187.2 x 174.4 x 145.8
