lucia-malickova/manta-chair/MANTA_RIBBON/02_SEG_00R.stl

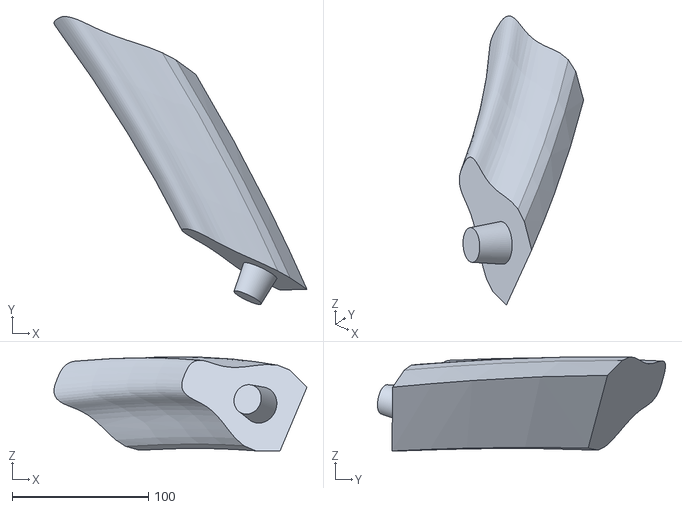
[picture p69: CAD file, 2026-09-29]
MANTA_RIBBON/02_SEG_00R.stl
185.8 x 211.5 x 69.0
