lucia-malickova/manta-chair/MANTA_LIGHT/14_SEG_06R.stl

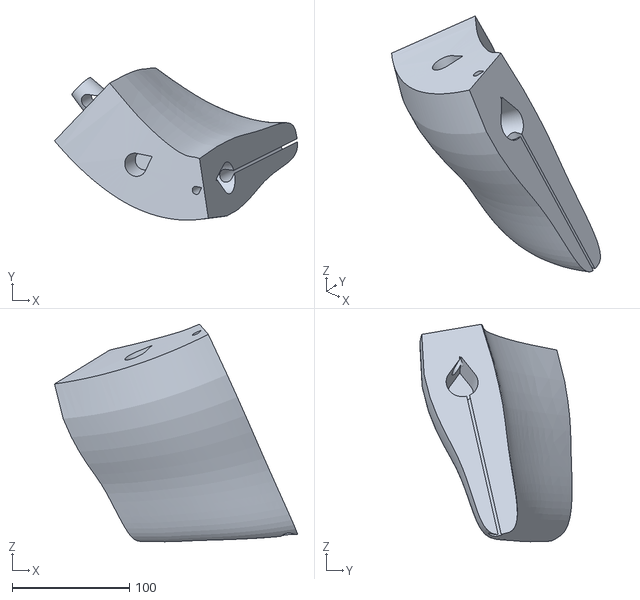
[picture p70: CAD file, 2026-09-29]
MANTA_LIGHT/14_SEG_06R.stl
207.6 x 130.0 x 185.9
