lucia-malickova/manta-chair/MANTA_RIBBON/05_SEG_02L.stl

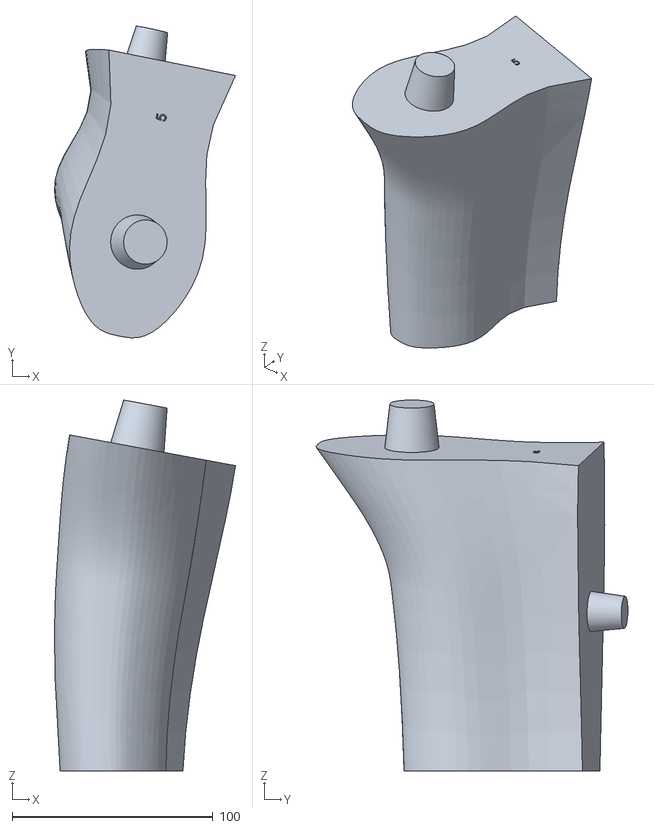
[picture p71: CAD file, 2026-09-29]
MANTA_RIBBON/05_SEG_02L.stl
90.1 x 155.2 x 184.7
