lucia-malickova/manta-chair/MANTA_LIGHT/39_SEG_21R.stl

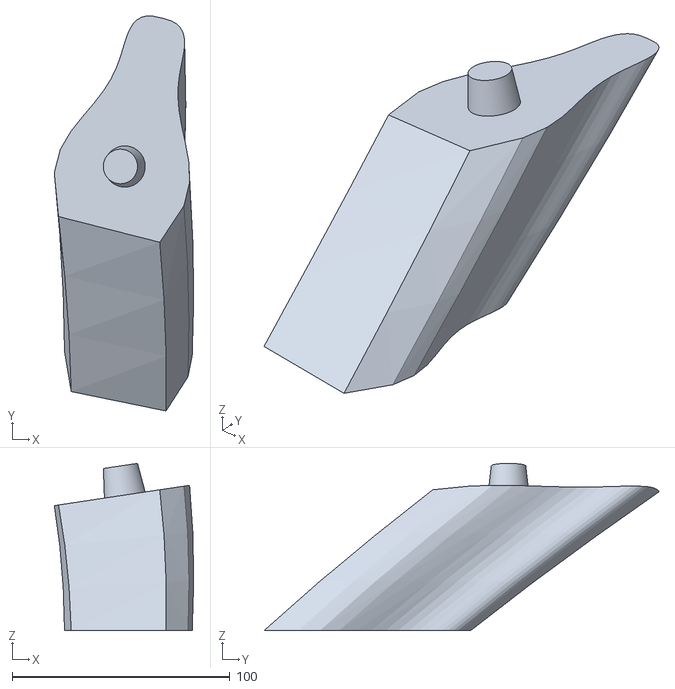
[picture p72: CAD file, 2026-09-29]
MANTA_LIGHT/39_SEG_21R.stl
64.0 x 181.3 x 76.8
