lucia-malickova/manta-chair/MANTA_RIBBON/34_SEG_19L.stl

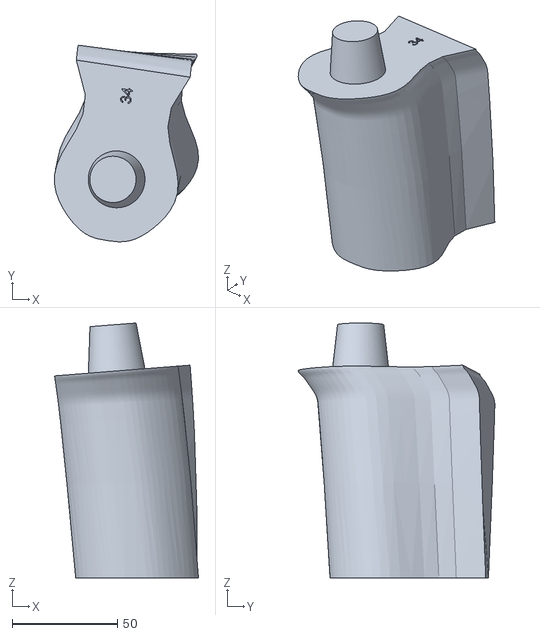
[picture p73: CAD file, 2026-09-29]
MANTA_RIBBON/34_SEG_19L.stl
68.5 x 93.5 x 121.2
