lucia-malickova/manta-chair/MANTA_LIGHT/31_SEG_16.stl

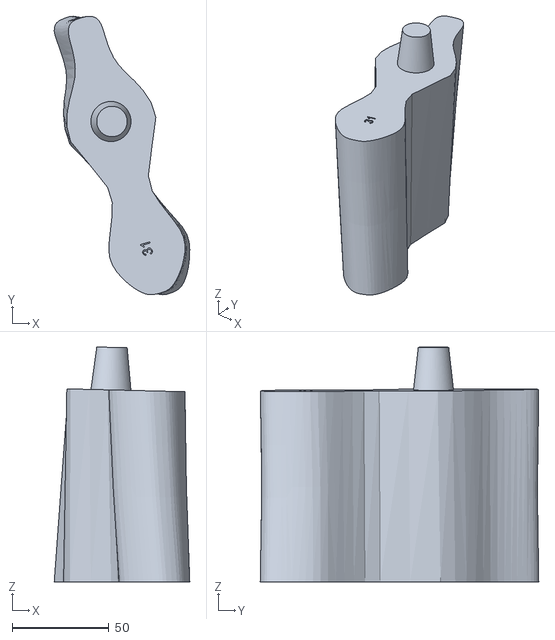
[picture p74: CAD file, 2026-09-29]
MANTA_LIGHT/31_SEG_16.stl
70.0 x 143.9 x 121.4
