lucia-malickova/manta-chair/MANTA_RIBBON/01_SEG_00L.stl

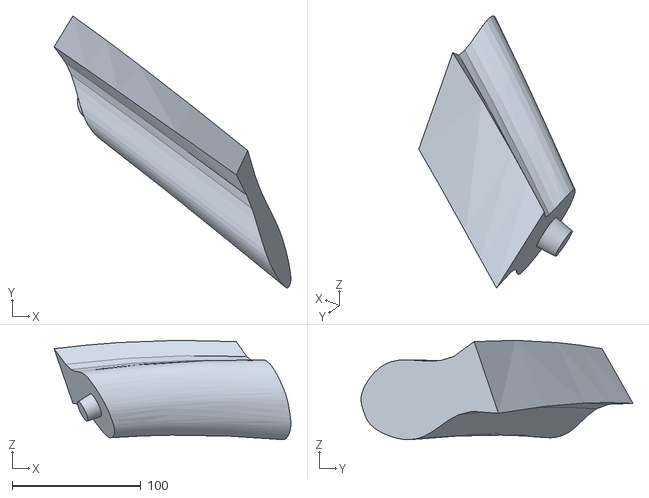
[picture p75: CAD file, 2026-09-29]
MANTA_RIBBON/01_SEG_00L.stl
184.0 x 211.3 x 77.1
