lucia-malickova/manta-chair/MANTA_LIGHT/13_SEG_06L.stl

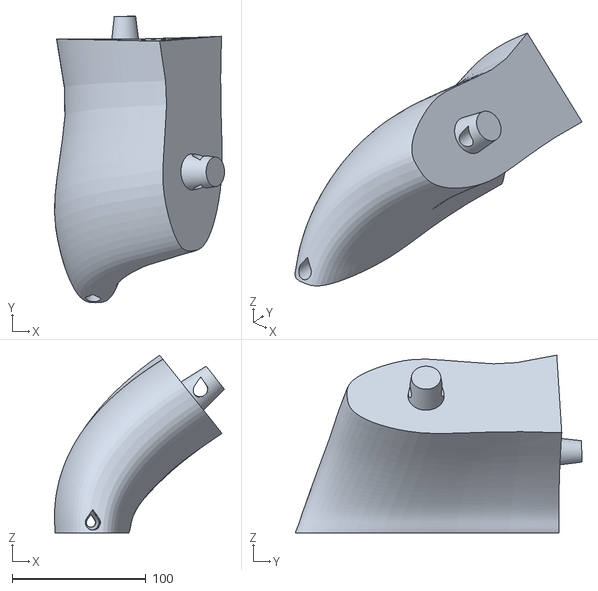
[picture p76: CAD file, 2026-09-29]
MANTA_LIGHT/13_SEG_06L.stl
127.0 x 214.0 x 132.7
