lucia-malickova/manta-chair/MANTA_RIBBON/40_SEG_22L.stl

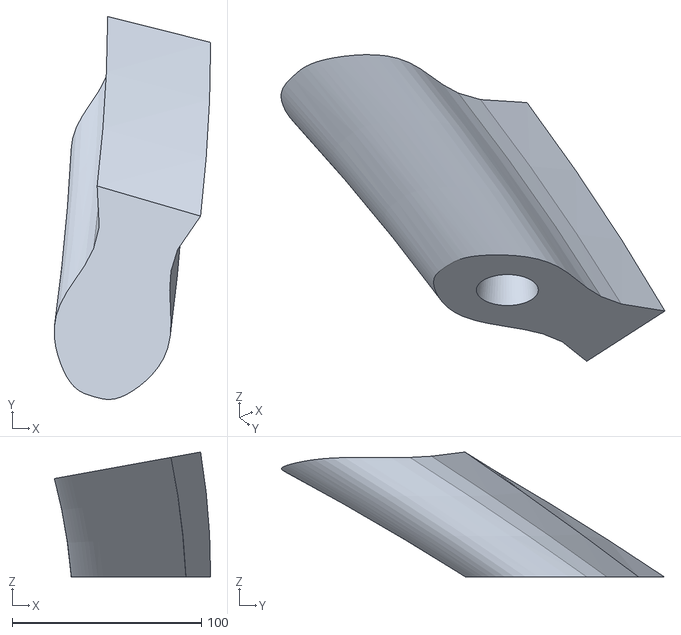
[picture p77: CAD file, 2026-09-29]
MANTA_RIBBON/40_SEG_22L.stl
82.5 x 202.3 x 66.0
