lucia-malickova/manta-chair/MANTA_LIGHT/12_SEG_05R.stl

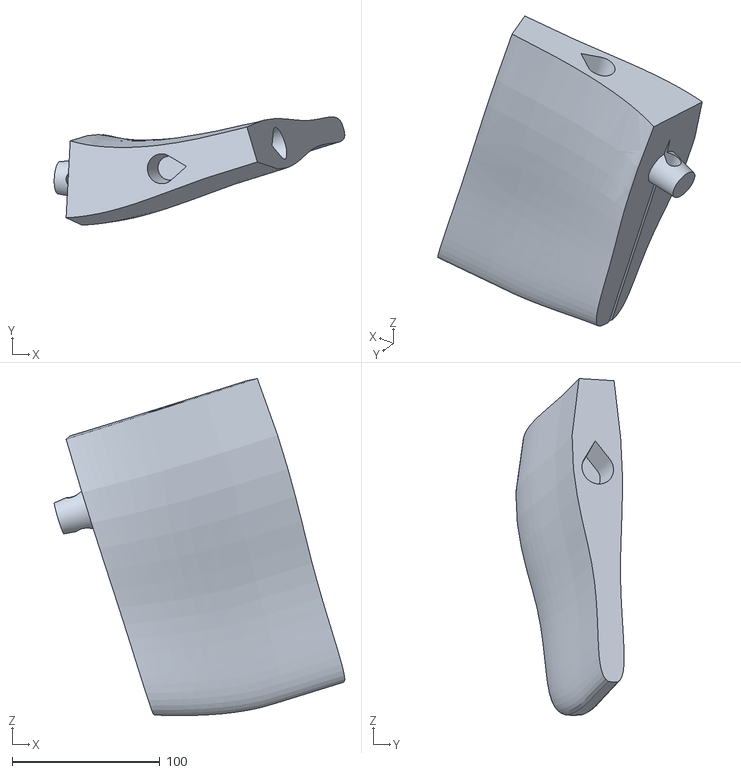
[picture p78: CAD file, 2026-09-29]
MANTA_LIGHT/12_SEG_05R.stl
196.8 x 73.3 x 228.2
