lucia-malickova/manta-chair/MANTA_RIBBON/31_SEG_16.stl

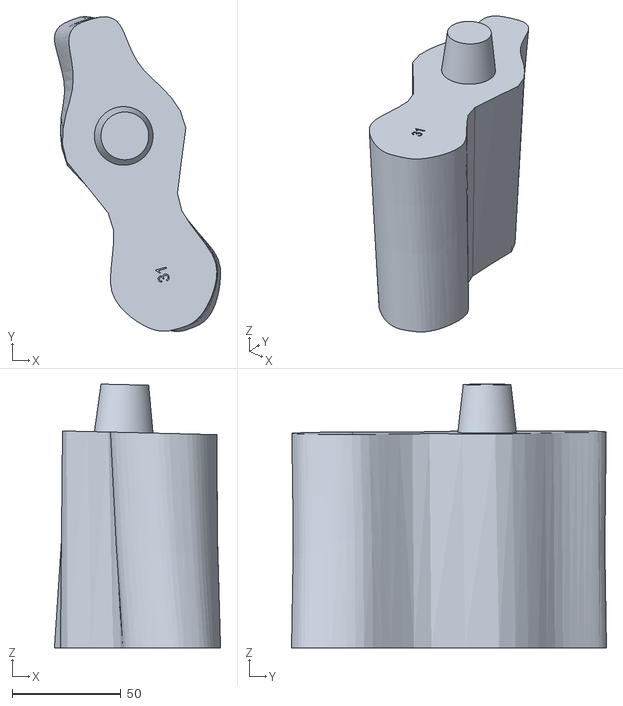
[picture p79: CAD file, 2026-09-29]
MANTA_RIBBON/31_SEG_16.stl
76.5 x 145.0 x 121.5
