lucia-malickova/manta-chair/MANTA_LIGHT/35_SEG_19R.stl

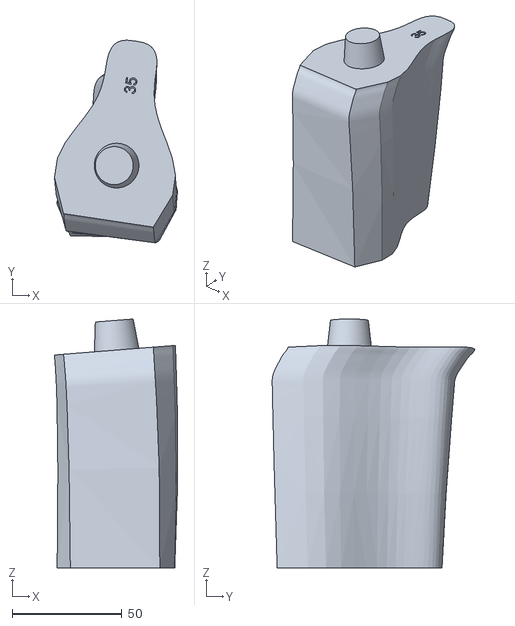
[picture p80: CAD file, 2026-09-29]
MANTA_LIGHT/35_SEG_19R.stl
56.1 x 92.4 x 113.5
