lucia-malickova/manta-chair/MANTA_RIBBON/03_SEG_01L.stl

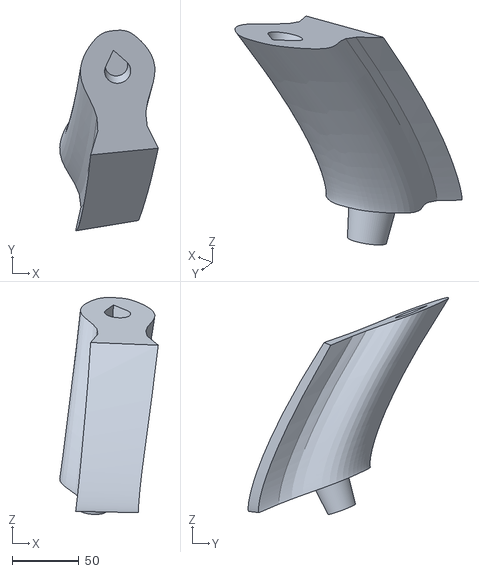
[picture p81: CAD file, 2026-09-29]
MANTA_RIBBON/03_SEG_01L.stl
73.8 x 150.2 x 162.3
