lucia-malickova/manta-chair/MANTA_LIGHT/30_SEG_15.stl

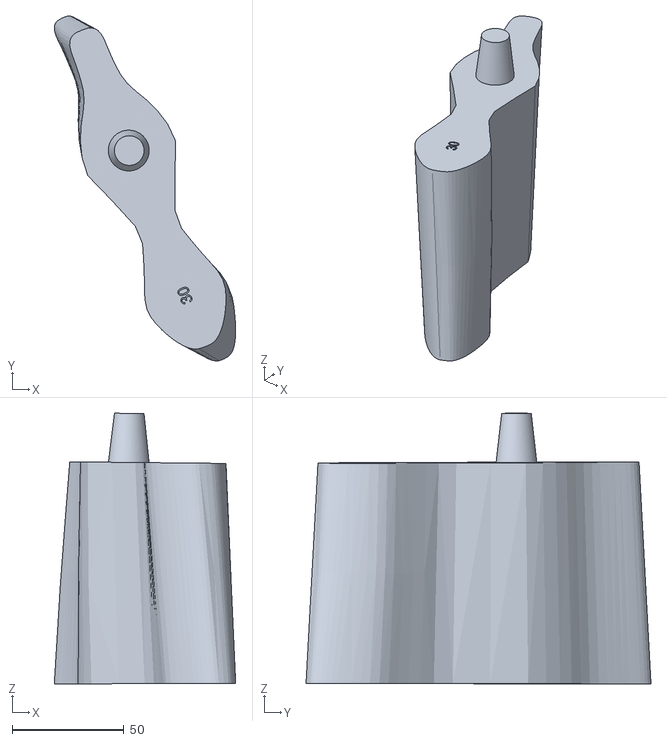
[picture p82: CAD file, 2026-09-29]
MANTA_LIGHT/30_SEG_15.stl
81.3 x 154.6 x 121.3
