lucia-malickova/manta-chair/MANTA_RIBBON/25_SEG_12L.stl

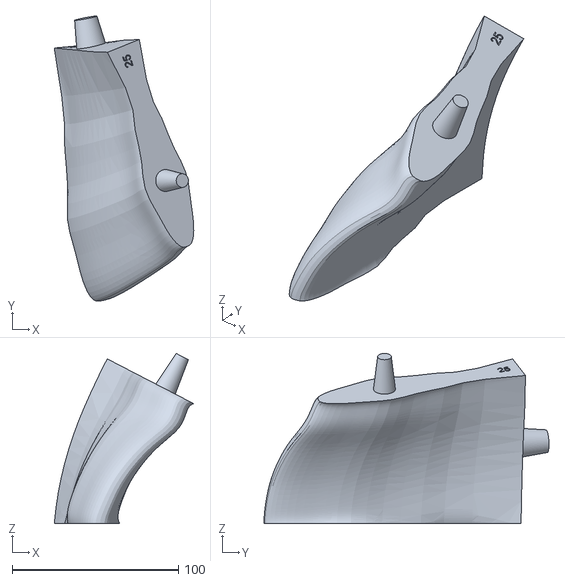
[picture p83: CAD file, 2026-09-29]
MANTA_RIBBON/25_SEG_12L.stl
84.0 x 171.6 x 102.4
