lucia-malickova/manta-chair/MANTA_RIBBON/12_SEG_05R.stl

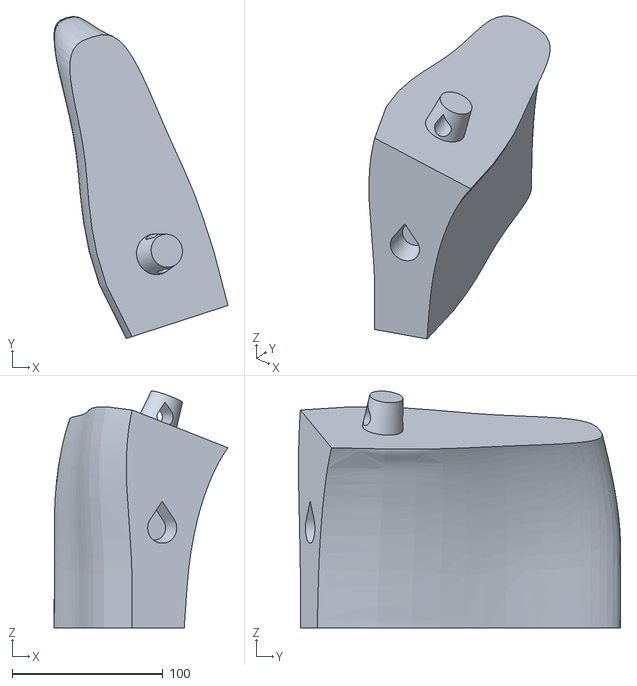
[picture p84: CAD file, 2026-09-29]
MANTA_RIBBON/12_SEG_05R.stl
115.3 x 213.3 x 156.9
