lucia-malickova/manta-chair/MANTA_LIGHT/29_SEG_14.stl

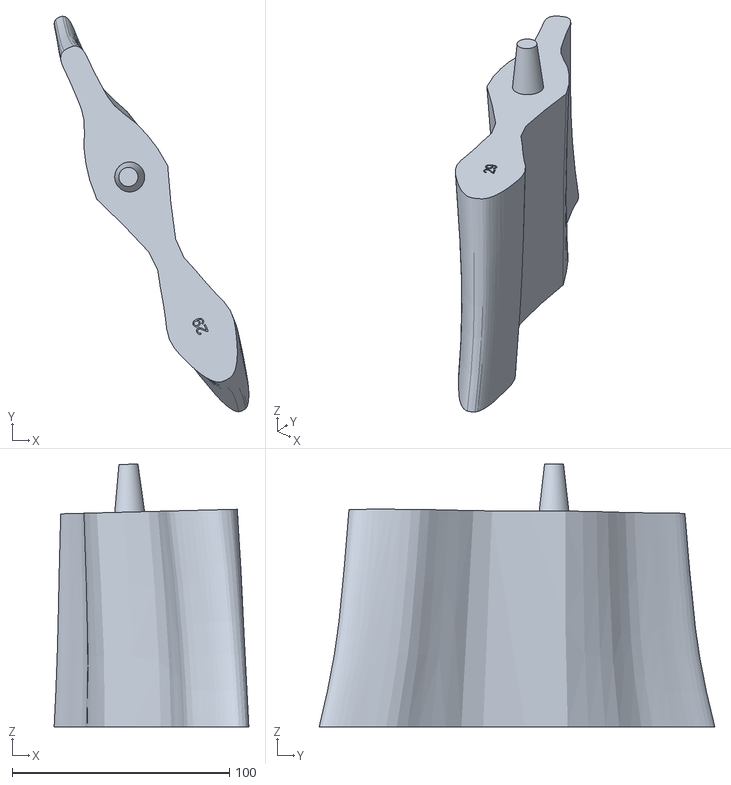
[picture p85: CAD file, 2026-09-29]
MANTA_LIGHT/29_SEG_14.stl
89.6 x 182.1 x 121.0
