lucia-malickova/manta-chair/MANTA_RIBBON/08_SEG_03R.stl

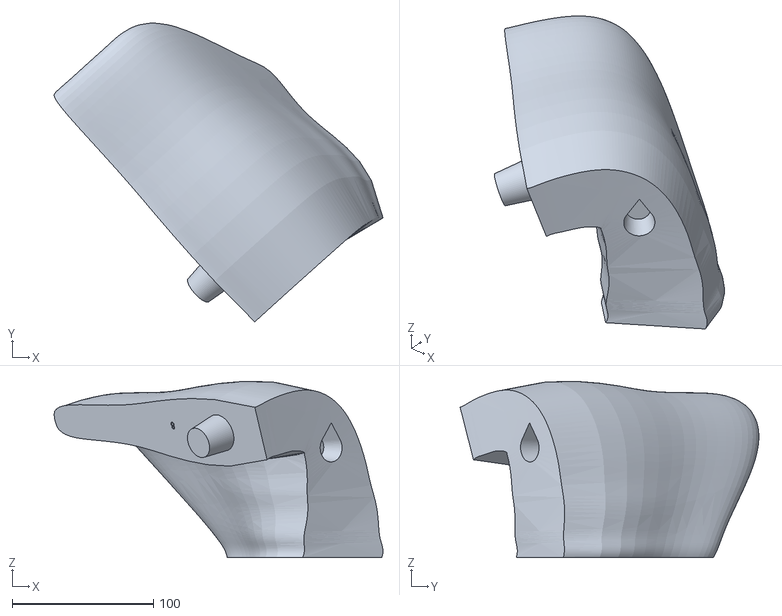
[picture p86: CAD file, 2026-09-29]
MANTA_RIBBON/08_SEG_03R.stl
233.3 x 211.8 x 125.0
